sjorsansems/retro-alarm-clock/animations/beegees.gif

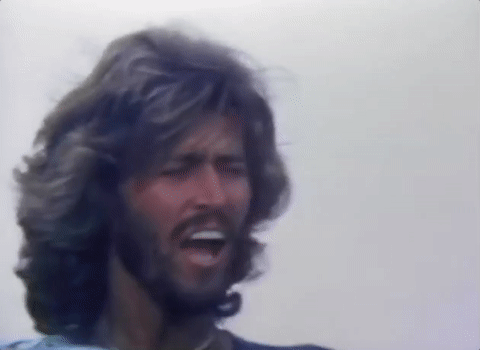
animations/beegees.gif
