sjorsansems/retro-alarm-clock/animations/fight.gif

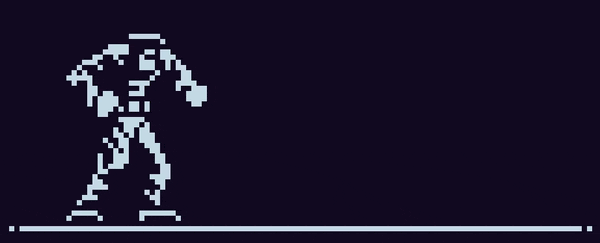
animations/fight.gif
