sjorsansems/retro-alarm-clock/animations/mk.gif

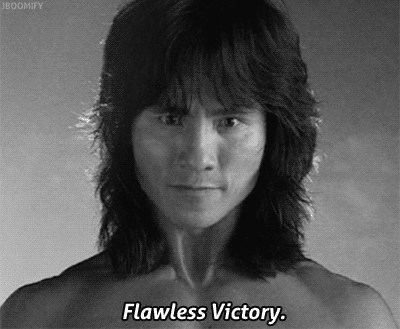
animations/mk.gif
