sjorsansems/retro-alarm-clock/retro_georgy_alarm_klok_v6_backup.py

"""
ESP32 Retro Georgy Alarm Clock (MicroPython)
Doel: stabiel draaien op lage RAM met WiFi + NTP + retro web UI + alarm animaties.
"""

from machine import Pin, SoftI2C
import framebuf
import time
import json
import network
import socket
import gc
import esp32

try:
    from urllib.parse import quote
except ImportError:
    quote = None

# Agressieve garbage collection en PSRAM setup
gc.enable()
gc.collect()
try:
    esp32.memory_info()
except:
    pass
try:
    gc.threshold(gc.mem_free() // 4 + gc.mem_alloc())
except:
    pass

LOW_MEMORY_WEB_MODE = False

# WLAN lazy init — niet pre-alloceren
_WLAN = None

try:
    from config_manager import ConfigManager
except ImportError:
    ConfigManager = None

try:
    from ntp_time_sync import NTPTimeSync
except ImportError:
    NTPTimeSync = None

try:
    from ds3231 import DS3231, AT24C32
except ImportError:
    DS3231 = None
    AT24C32 = None

try:
    from dfplayer import DFPlayer
except ImportError:
    DFPlayer = None

try:
    from neopixel_driver import NeopixelDriver
except ImportError:
    NeopixelDriver = None

# ESP32-S3 DevKitC-1 pinnen
SDA_PIN = 8   # gelabeld SDA op het board (OLED)
SCL_PIN = 9   # gelabeld SCL op het board (OLED)
DS3231_SDA_PIN = 5   # aparte I2C bus voor DS3231 RTC
DS3231_SCL_PIN = 6
I2C_FREQ = 100_000
# Buzzer uitgeschakeld — DFPlayer MP3 wordt gebruikt als alarm

# DFPlayer Mini: ESP32-S3 DevKitC-1
# GPIO17 = UART1 TX (gelabeld TXD1) -> 1kΩ -> DFPlayer RX
# GPIO18 = UART1 RX (gelabeld RXD1) <--------- DFPlayer TX
# Optioneel: BUSY-pin (actief-laag als er afgespeeld wordt)
DFPLAYER_UART_ID  = 1
DFPLAYER_TX_PIN   = 17
DFPLAYER_RX_PIN   = 18
DFPLAYER_BUSY_PIN = None   # bijv. 4 als je de BUSY-pin aansluit
DFPLAYER_TRACK    = 1      # track-nummer dat tijdens alarm afgespeeld wordt (1.mp3 op SD)

# WS2812B Addressable LEDs (8-LED strip)
WS2812_PIN = 2  # bevestigd werkend: GPIO2 + bitstream + GRB
WS2812_COUNT = 8  # 8 LEDs
WIDTH = 128
HEIGHT = 64
SH1106_COL_OFFSET = 2
WIFI_PORT = 80
WEBSERVER_START_DELAY_MS = 0
WIFI_MANUAL_ON_MS = 120000
WIFI_DAILY_CHECK_MS = 60000
WIFI_DAILY_RETRY_MS = 3600000
WIFI_MIN_FREE_HEAP = 35000
WIFI_CONNECT_TIMEOUT_S = 8
DEFAULT_WIFI_SSID = ""
WIFI_HOSTNAME = "alarmklok"
ALARM_INTRO_MS = 2500
ALARM_BOSS_MS = 20000
ALARM_AUTO_STOP_MS = 15 * 60 * 1000
NIGHT_DIM_START_HOUR = 22
NIGHT_DIM_END_HOUR = 7
UP_BUTTON_PIN = 13    # Touch13 / ADC2_2 — vrij op S3 DevKitC-1
DOWN_BUTTON_PIN = 12  # Touch12 / ADC2_1 — vrij
SET_BUTTON_PIN = 14   # Touch14 / ADC2_3 — vrij
DAY_KEYS = ("mon", "tue", "wed", "thu", "fri", "sat", "sun")

# Aantal MP3-nummers op de SD-kaart (lied 1 t/m N)
DFPLAYER_TRACK_COUNT = 30

# Koppel GIF-namen aan een alarm-tone (muziek + LEDs).
# Voeg hier nieuwe GIFs toe die je aan een specifiek liedje wilt koppelen.
# Waarde None = geen koppeling, gebruiker kiest zelf tone.
GIF_TONE_MAP = {
    "mario": "2",
    "zelda": "1",
    "doom":  None,
}


def get_alarm_tone_options():
    labels = {
        1: "Zelda", 2: "Mario", 3: "Synthwave", 4: "Sonic", 
        5: "Metroid", 6: "Pokemon", 7: "Tetris", 8: "Moonstone", 9: "Arcade"
    }
    schemes = {
        1: "Groen -> goud pulse",
        2: "Rood/geel checker",
        3: "Neon roze -> paars golf",
        4: "Cyaan/blauw strobe",
        5: "Oranje -> rood",
        6: "Geel met rode accenten",
        7: "Regenboog cyclus",
        8: "Maanblauw met fakkel-goud pulse",
        9: "Multicolor strobe",
    }
    return [
        {
            "key": str(i),
            "label": labels.get(i, "Lied {}".format(i)),
            "scheme": schemes.get(i, "Onbekend"),
        }
        for i in range(1, DFPLAYER_TRACK_COUNT + 1)
    ]


BIG_TIME_GLYPHS = {
    "0": ("111", "101", "101", "101", "111"),
    "1": ("010", "110", "010", "010", "111"),
    "2": ("111", "001", "111", "100", "111"),
    "3": ("111", "001", "111", "001", "111"),
    "4": ("101", "101", "111", "001", "001"),
    "5": ("111", "100", "111", "001", "111"),
    "6": ("111", "100", "111", "101", "111"),
    "7": ("111", "001", "001", "001", "001"),
    "8": ("111", "101", "111", "101", "111"),
    "9": ("111", "101", "111", "001", "111"),
    ":": ("0", "1", "0", "1", "0"),
}

_HTML_FILE = "index_v6.html"
_HTML_FILE_LITE = "index_lite.html"


def _send_all(sock, data):
    view = memoryview(data)
    while len(view):
        sent = sock.send(view)
        if sent is None or sent <= 0:
            break
        view = view[sent:]


def _send_html_response(sock, filename):
    _send_all(sock, b"HTTP/1.1 200 OK\r\nContent-Type: text/html\r\nConnection: close\r\n\r\n")
    try:
        with open(filename, "rb") as f:
            while True:
                chunk = f.read(512)
                if not chunk:
                    break
                _send_all(sock, chunk)
    except Exception as e:
        body = "<html><body>Fout: kan {} niet laden: {}</body></html>".format(filename, e)
        _send_all(sock, body.encode())


# HTML wordt van disk naar socket gestreamd via _send_html_response() - niet in RAM opgeslagen.
def enable_low_memory_web_mode():
    global LOW_MEMORY_WEB_MODE
    if LOW_MEMORY_WEB_MODE:
        return
    LOW_MEMORY_WEB_MODE = True
    gc.collect()


class SH1106_I2C(framebuf.FrameBuffer):
    def __init__(self, width, height, i2c, addr=0x3C):
        self.width = width
        self.height = height
        self.i2c = i2c
        self.addr = addr
        self.pages = height // 8
        self.buffer = bytearray(self.pages * width)
        super().__init__(self.buffer, width, height, framebuf.MONO_VLSB)
        for cmd in (0xAE, 0xD5, 0x80, 0xA8, self.height - 1, 0xD3, 0x00, 0x40,
                    0xAD, 0x8B, 0xA1, 0xC8, 0xDA, 0x12, 0x81, 0x7F, 0xD9, 0x22,
                    0xDB, 0x35, 0xA4, 0xA6, 0xAF):
            self.i2c.writeto(self.addr, bytes((0x80, cmd)))
        self.fill(0)
        self.show()

    def show(self):
        for page in range(self.pages):
            self.i2c.writeto(self.addr, bytes((0x80, 0xB0 + page)))
            col = SH1106_COL_OFFSET
            self.i2c.writeto(self.addr, bytes((0x80, col & 0x0F)))
            self.i2c.writeto(self.addr, bytes((0x80, 0x10 | (col >> 4))))
            start = self.width * page
            self.i2c.writeto(self.addr, b"\x40" + self.buffer[start:start + self.width])


class WiFiManagerLite:
    def __init__(self, ssid, password, timeout=WIFI_CONNECT_TIMEOUT_S):
        self.ssid = ssid
        self.password = password
        self.timeout = timeout
        global _WLAN
        if _WLAN is None:
            # Agressieve RAM cleanup voordat WiFi wordt geladen
            for _ in range(3):
                gc.collect()
                time.sleep(0.1)
            try:
                _WLAN = network.WLAN(network.STA_IF)
                # WLAN voorbij initi, nog niet actief
            except Exception as e:
                print("! WiFi pre-init fout, retrying...")
                for _ in range(5):
                    gc.collect()
                    time.sleep(0.1)
                try:
                    _WLAN = network.WLAN(network.STA_IF)
                except Exception:
                    raise OSError("WiFi Out of Memory")
        self.sta = _WLAN

    def connect(self):
        try:
            if self.sta.isconnected():
                return True
        except:
            pass

        if not self.ssid:
            print("! WiFi fout: SSID is leeg")
            return False

        try:
            # Minder agressief dan telkens active(False)->active(True),
            # want dat kan op sommige firmware builds instabiel zijn.
            if not self.sta.active():
                self.sta.active(True)
            time.sleep(0.5)

            # Zet een herkenbare netwerknaam voor DHCP/local DNS waar ondersteund.
            try:
                self.sta.config(dhcp_hostname=WIFI_HOSTNAME)
                print("WiFi hostname:", WIFI_HOSTNAME)
            except Exception:
                try:
                    network.hostname(WIFI_HOSTNAME)
                    print("WiFi hostname:", WIFI_HOSTNAME)
                except Exception:
                    pass

            # Begin met een schone connect-staat.
            try:
                self.sta.disconnect()
            except:
                pass

            print("WiFi: verbinden met '{}'...".format(self.ssid))
            self.sta.connect(self.ssid, self.password)
            start = time.ticks_ms()
            while not self.sta.isconnected():
                st = self.sta.status()
                # ESP32 statuscodes: -3 wrong password, -2 no AP, -1 fail
                if st in (-3, -2, -1):
                    if st == -3:
                        print("! WiFi fout: verkeerd wachtwoord")
                    elif st == -2:
                        print("! WiFi fout: SSID niet gevonden (2.4GHz?)")
                    else:
                        print("! WiFi fout: connect mislukt")
                    return False
                if time.ticks_diff(time.ticks_ms(), start) > self.timeout * 1000:
                    print("! WiFi timeout na {}s, status={}".format(self.timeout, self.sta.status()))
                    return False
                time.sleep(0.3)
                gc.collect()  # Agressieve GC tijdens connect
            ip = self.sta.ifconfig()[0]
            print("✓ WiFi verbonden, IP={}".format(ip))
            return True
        except KeyboardInterrupt:
            # Laat app doorlopen zonder crash als connect wordt onderbroken.
            print("! WiFi connect onderbroken")
            try:
                self.sta.disconnect()
            except:
                pass
            return False
        except Exception as e:
            print("! WiFi connect fout:", e)
            gc.collect()
            return False

    def is_connected(self):
        try:
            return self.sta and self.sta.isconnected()
        except:
            return False

    def get_ip(self):
        try:
            if self.is_connected():
                return self.sta.ifconfig()[0]
        except:
            pass
        return None


class ClockCore:
    def __init__(self, timezone_name="Europe/Amsterdam"):
        self.timezone_name = timezone_name
        self.soft_epoch = None
        self.soft_ticks = 0
        self.last_sync = 0
        self.rtc = None  # wordt gezet door App na I2C init

    @staticmethod
    def _is_leap_year(year):
        return (year % 4 == 0 and year % 100 != 0) or (year % 400 == 0)

    @staticmethod
    def _last_sunday_of_month(year, month):
        if month in (1, 3, 5, 7, 8, 10, 12):
            last_day = 31
        elif month in (4, 6, 9, 11):
            last_day = 30
        else:
            last_day = 29 if ClockCore._is_leap_year(year) else 28
        for day in range(last_day, 0, -1):
            wd = time.localtime(time.mktime((year, month, day, 12, 0, 0, 0, 0)))[6]  # 0=ma
            if wd == 6:  # zondag
                return day
        return last_day

    @staticmethod
    def _is_dst_nl(year, month, day):
        if month < 3 or month > 10:
            return False
        if 3 < month < 10:
            return True
        if month == 3:
            return day >= ClockCore._last_sunday_of_month(year, 3)
        return day < ClockCore._last_sunday_of_month(year, 10)

    @staticmethod
    def _utc_to_amsterdam(utc_tuple):
        y, m, d, hh, mm, ss = utc_tuple[:6]
        offset = 2 if ClockCore._is_dst_nl(y, m, d) else 1
        base = (y, m, d, hh, mm, ss, 0, 0)
        shifted = time.localtime(time.mktime(base) + offset * 3600)
        return (shifted[0], shifted[1], shifted[2], shifted[3], shifted[4], shifted[5], shifted[6] + 1, shifted[7])

    def _tz(self, utc_tuple):
        if self.timezone_name == "Europe/Amsterdam" and NTPTimeSync:
            t = NTPTimeSync.time_tuple_to_dutch(utc_tuple)
            if len(t) >= 7:
                t = t[:6] + (t[6] + 1,) + t[7:]
            return t, ("CEST" if NTPTimeSync.is_dst(utc_tuple[0], utc_tuple[1], utc_tuple[2]) else "CET")
        if self.timezone_name == "Europe/Amsterdam":
            t = self._utc_to_amsterdam(utc_tuple)
            return t, ("CEST" if self._is_dst_nl(utc_tuple[0], utc_tuple[1], utc_tuple[2]) else "CET")
        off = 0
        if self.timezone_name.startswith("UTC") and len(self.timezone_name) > 3:
            try:
                off = int(self.timezone_name[3:])
            except:
                off = 0
        base = (utc_tuple[0], utc_tuple[1], utc_tuple[2], utc_tuple[3], utc_tuple[4], utc_tuple[5], 0, 0)
        shifted = time.localtime(time.mktime(base) + off * 3600)
        return (shifted[0], shifted[1], shifted[2], shifted[3], shifted[4], shifted[5], shifted[6] + 1, shifted[7]), ("UTC" if off == 0 else "UTC{}{}".format("+" if off > 0 else "", off))

    def read_time(self):
        # Lees bij voorkeur rechtstreeks van DS3231
        if self.rtc is not None:
            try:
                t = self.rtc.datetime()   # (yr, mo, day, hr, min, sec, wd)
                # DS3231 bewaart in deze app al lokale tijd; niet opnieuw timezone-shiften.
                return (t[0], t[1], t[2], t[3], t[4], t[5], t[6], 0)
            except Exception:
                pass
        if self.soft_epoch is None:
            utc = time.gmtime()
            t, _ = self._tz(utc)
            self.set_time(*t[:6])
            return t
        elapsed = time.ticks_diff(time.ticks_ms(), self.soft_ticks) // 1000
        cur = time.localtime(self.soft_epoch + elapsed)
        return (cur[0], cur[1], cur[2], cur[3], cur[4], cur[5], cur[6] + 1, cur[7])

    def set_time(self, y, m, d, hh, mm, ss):
        base = (int(y), int(m), int(d), int(hh), int(mm), int(ss), 0, 0)
        self.soft_epoch = time.mktime(base)
        self.soft_ticks = time.ticks_ms()
        # Schrijf ook naar DS3231 als die beschikbaar is
        if self.rtc is not None:
            try:
                import time as _t
                wd = _t.localtime(self.soft_epoch)[6] + 1  # 1=ma
                self.rtc.set_datetime(int(y), int(m), int(d), int(hh), int(mm), int(ss), wd)
            except Exception as _e:
                print("! DS3231 schrijven mislukt:", _e)
        return True

    def set_timezone(self, name):
        self.timezone_name = name or "Europe/Amsterdam"
        utc = time.gmtime()
        t, _ = self._tz(utc)
        self.set_time(*t[:6])

    def sync_ntp(self):
        try:
            import ntptime
            ntptime.host = "pool.ntp.org"
            ntptime.settime()
            utc = time.gmtime()
            t, label = self._tz(utc)
            self.set_time(*t[:6])
            self.last_sync = time.time()
            print("✓ NTP Sync ({}) → ook naar DS3231 geschreven".format(label) if self.rtc else "✓ NTP Sync ({})".format(label))
            return True
        except Exception as e:
            print("✗ NTP Sync fout:", e)
            return False

    def timezone_label(self):
        t = self.read_time()
        if self.timezone_name == "Europe/Amsterdam" and NTPTimeSync:
            return "CEST" if NTPTimeSync.is_dst(t[0], t[1], t[2]) else "CET"
        return self.timezone_name


class App:
    def __init__(self):
        print("\n=== ESP32 RETRO GEORGY ALARM OPSTARTEN ===\n")
        self.config = ConfigManager("config.json") if ConfigManager else None
        self.tone = "1"
        self.volume = 70
        wifi_source = "fallback"
        if self.config:
            self.tone = self.config.get("alarm_sound", "tone", "1")
            self.volume = int(self.config.get("alarm_sound", "volume", 70) or 70)
            timezone = self.config.get("ntp", "timezone", "Europe/Amsterdam")
            raw_ssid = self.config.get("wifi", "ssid", None)
            raw_pwd = self.config.get("wifi", "password", None)
            ssid = str(raw_ssid or "").strip()
            pwd = str(raw_pwd or "")
            if ssid:
                wifi_source = "config.json"
            if getattr(self.config, "last_load_error", None):
                print("! Config waarschuwing:", self.config.last_load_error)
        else:
            timezone, ssid, pwd = "Europe/Amsterdam", "", ""

        if not ssid:
            ssid = DEFAULT_WIFI_SSID
            wifi_source = "defaults"

        print("WiFi cfg: '{}' ({})".format(ssid, wifi_source))
        self.wifi_ssid = ssid
        self.wifi_password = pwd
        self.tone = self._normalize_tone_key(self.tone)

        self.clock = ClockCore(timezone)
        self.alarm_until = None
        self.alarm_started_ms = None
        self.snooze_until = None
        self.snooze_tone = None
        self.snooze_gif = ""
        self.active_tone = self.tone
        self.active_gif = ""
        self._skip_intro = False
        self._in_intro = False
        self.alarm_edit_mode = False
        self.alarm_edit_last_change_ms = 0
        self.alarm_edit_hold_hint_until = 0
        self.alarm_edit_hour = 7
        self.alarm_edit_minute = 0
        self.alarm_edit_day_key = "mon"
        self._set_toggle_last_key = None
        self._set_feedback_text = ""
        self._set_feedback_until = 0
        self._set_feedback_lines = []
        self._intro_audio_playing = False
        self.last_schedule_fire = None
        self.alarm_schedule = self._default_alarm_schedule()
        if self.config:
            self.alarm_schedule = self._normalize_alarm_schedule(self.config.get("alarm_schedule", None, self.alarm_schedule))
        self.alarm_combo = self._default_alarm_combo()
        if self.config:
            self.alarm_combo = self._normalize_alarm_combo(self.config.get("alarm_combo", None, self.alarm_combo))
        self.alarm_gif_combo = self._default_alarm_gif_combo()
        if self.config:
            self.alarm_gif_combo = self._normalize_alarm_gif_combo(self.config.get("alarm_gif_combo", None, self.alarm_gif_combo))

        # GIF → toon koppeling (instelbaar via webinterface, opgeslagen in gif_tone_map.json)
        self._gif_tone_overrides = {}
        try:
            with open("gif_tone_map.json", "r") as _f:
                self._gif_tone_overrides = json.loads(_f.read())
        except Exception:
            pass

        # Track labels (instelbaar via webinterface, opgeslagen in track_labels.json)
        self._track_labels = {}
        try:
            with open("track_labels.json", "r") as _f:
                self._track_labels = json.loads(_f.read())
        except Exception:
            pass

        self.wifi = None
        self.wifi_ok = False
        self.wifi_disabled = False
        self.wifi_reconnect_after_ms = 0
        self.wifi_auto_off_ms = time.ticks_add(time.ticks_ms(), 30 * 60 * 1000)
        self.webserver_ready_after_ms = None
        self._ntp_synced_once = False
        self.startup_ip_until = None
        self.sock = None
        self.wifi_manual_until = None
        self.last_daily_sync_key = None
        self.next_daily_check_ms = time.ticks_add(time.ticks_ms(), WIFI_DAILY_CHECK_MS)
        self.next_daily_sync_attempt_ms = time.ticks_ms()
        self._display_dim_state = None
        self._display_manual_mode = 0  # 0=normaal, 1=dim, 2=extra dim
        self._weather_phase = 0
        self._rtc_temp = None
        self._rtc_temp_next_ms = 0
        self._weather_code = None      # WMO weathercode van Open-Meteo
        self._weather_temp = None      # buitentemperatuur °C (int)
        self._weather_next_ms = 0      # tijdstip eerste fetch (meteen bij opstart)
        self._weather_interval_ms = 6 * 3600 * 1000  # 4x per dag
        self._easter_active_until = None
        self._easter_message = ""
        self._easter_key = None
        # Klok-transitie animatie state
        self._transition_pending = True   # eerste keer na intro altijd animeren
        self._last_hour_shown = -1        # voor uur-omslag detectie
        self._transition_step = 0         # huidige frame binnen een lopende transitie
        self._transition_id = 0           # welke transitie (0-4)
        self._transition_active = False   # animatie bezig?
        self._transition_use_leds = True  # LEDs bij deze transitie? (False bij uur-omslag)
        self._transition_buf = None       # snapshot van klokscherm (bytearray 128×64/8)

        self.i2c = SoftI2C(sda=Pin(SDA_PIN, pull=Pin.PULL_UP), scl=Pin(SCL_PIN, pull=Pin.PULL_UP), freq=I2C_FREQ)
        self.display = None
        try:
            dev = self.i2c.scan()
            if 0x3C in dev:
                self.display = SH1106_I2C(WIDTH, HEIGHT, self.i2c, 0x3C)
        except:
            pass

        # DS3231 RTC initialiseren op eigen I2C bus (GPIO5/6)
        self.eeprom = None
        self.i2c_rtc = None
        if DS3231 is not None:
            try:
                self.i2c_rtc = SoftI2C(sda=Pin(DS3231_SDA_PIN, pull=Pin.PULL_UP), scl=Pin(DS3231_SCL_PIN, pull=Pin.PULL_UP), freq=I2C_FREQ)
                self.clock.rtc = DS3231(self.i2c_rtc)
                t = self.clock.rtc.datetime()
                print("✓ DS3231 gereed: {:04d}-{:02d}-{:02d} {:02d}:{:02d}:{:02d}".format(*t[:6]))
            except Exception as _e:
                print("! DS3231 niet gevonden:", _e)
                self.clock.rtc = None

        # AT24C32 EEPROM initialiseren (op dezelfde I2C bus als DS3231)
        if self.i2c_rtc is not None and AT24C32 is not None:
            try:
                self.eeprom = AT24C32(self.i2c_rtc)
                eeprom_schedule = self.eeprom.load_alarm_schedule()
                if eeprom_schedule is not None:
                    self.alarm_schedule = self._normalize_alarm_schedule(eeprom_schedule)
                    print("✓ Alarmschema geladen uit EEPROM")
                else:
                    print("✓ AT24C32 gereed (geen opgeslagen schema)")
            except Exception as _e:
                print("! AT24C32 niet gevonden:", _e)
                self.eeprom = None

        # DFPlayer/WS2812 lazy init: pas initialiseren zodra alarm start.
        self.dfplayer = None
        self._dfplayer_failed = False
        self._dfplayer_playing = False

        self.leds = None
        self._leds_failed = False
        self._led_sunrise_active = False
        self._nightlight_on = False

        # GIF-animatie state (alarm)
        self._gif_file = None
        self._gif_n_frames = 0
        self._gif_frame_size = 0
        self._gif_delays = []
        self._gif_cur_frame = 0
        self._gif_next_ms = 0
        self._gif_data_offset = 0

        # Zorg dat de strip direct bij boot in een bekende UIT-toestand staat.
        self._ensure_leds_ready()
        if self.leds is not None:
            try:
                self.leds.clear()
            except Exception:
                pass

        self.btn_up = Pin(UP_BUTTON_PIN, Pin.IN, Pin.PULL_UP)
        self.btn_down = Pin(DOWN_BUTTON_PIN, Pin.IN, Pin.PULL_UP)
        self.btn_set = Pin(SET_BUTTON_PIN, Pin.IN, Pin.PULL_UP)
        # start=tijdstip indrukken, fired_long=lange druk al uitgevoerd,
        # last_edge=debounce timestamp, pending=actie klaar voor uitvoering
        self._button_state = {
            "set":  {"start": 0, "fired_long": False, "last_edge": 0, "pending": None},
            "up":   {"start": 0, "fired_long": False, "last_edge": 0, "pending": None},
            "down": {"start": 0, "fired_long": False, "last_edge": 0, "pending": None},
        }

        # Hardware IRQ op falling + rising edge:
        # - UP heeft geen lange druk → vuurt pending="short" direct bij indrukken
        # - SET/DOWN wachten tot loslaten om te bepalen of het kort of lang was
        _bs = self._button_state
        def _make_irq(name, has_long_cb):
            s = _bs[name]
            def handler(p):
                now = time.ticks_ms()
                if time.ticks_diff(now, s["last_edge"]) < 40:
                    return
                s["last_edge"] = now
                if p.value() == 0:  # falling edge = ingedrukt
                    s["start"] = now
                    s["fired_long"] = False
                    if not has_long_cb:
                        s["pending"] = "short"  # direct actie op druk
                    # SET knop tijdens intro -> alleen overslaan (geen short/long actie na intro).
                    if name == "set" and self._in_intro:
                        self._skip_intro = True
                        s["pending"] = None
                        s["fired_long"] = True
                else:  # rising edge = losgelaten
                    if has_long_cb and not s["fired_long"]:
                        s["pending"] = "short"  # was een korte druk
            return handler
        self.btn_up.irq(trigger=Pin.IRQ_FALLING | Pin.IRQ_RISING, handler=_make_irq("up", False))
        self.btn_down.irq(trigger=Pin.IRQ_FALLING | Pin.IRQ_RISING, handler=_make_irq("down", True))
        self.btn_set.irq(trigger=Pin.IRQ_FALLING | Pin.IRQ_RISING, handler=_make_irq("set", True))

        print("WiFi: verbinden...")
        gc.collect()
        gc.collect()
        if self._ensure_wifi_connected():
            self.clock.sync_ntp()
            self._ntp_synced_once = True
            t2 = self.clock.read_time()
            self.last_daily_sync_key = (int(t2[0]), int(t2[1]), int(t2[2]))
        else:
            print("WiFi: niet verbonden bij opstarten")
        self._apply_display_brightness(force=True)

    def _prepare_for_wifi_attempt(self):
        gc.collect()
        gc.collect()
        gc.collect()

    def _ensure_dfplayer_ready(self):
        if self.dfplayer is not None or self._dfplayer_failed or DFPlayer is None:
            return self.dfplayer is not None
        try:
            dfvol = max(0, min(30, int(self.volume * 30 // 100)))
            self.dfplayer = DFPlayer(
                uart_id=DFPLAYER_UART_ID,
                tx_pin=DFPLAYER_TX_PIN,
                rx_pin=DFPLAYER_RX_PIN,
                busy_pin=DFPLAYER_BUSY_PIN,
                volume=dfvol,
            )
            print("✓ DFPlayer Mini gereed (volume {})".format(dfvol))
            return True
        except Exception as e:
            print("! DFPlayer init mislukt:", e)
            self._dfplayer_failed = True
            self.dfplayer = None
            gc.collect()
            return False

    def _ensure_leds_ready(self):
        if self.leds is not None or self._leds_failed or NeopixelDriver is None:
            return self.leds is not None
        try:
            self.leds = NeopixelDriver(pin=WS2812_PIN, num_leds=WS2812_COUNT)
            self.leds.set_brightness(92)  # 36% brightness om stroom-problemen te voorkomen
            self.leds.clear()
            print("✓ WS2812B LEDs gereed (GPIO{}, {} LEDs)".format(WS2812_PIN, WS2812_COUNT))
            return True
        except Exception as e:
            print("! WS2812B init mislukt:", e)
            self._leds_failed = True
            self.leds = None
            gc.collect()
            return False

    def _close_webserver(self):
        try:
            if self.sock:
                self.sock.close()
        except:
            pass
        self.sock = None

    def _disable_wifi(self):
        self._close_webserver()
        try:
            if self.wifi and self.wifi.sta:
                try:
                    self.wifi.sta.disconnect()
                except:
                    pass
                try:
                    self.wifi.sta.active(False)
                except:
                    pass
        except:
            pass
        self.wifi_ok = False

    def _ensure_wifi_connected(self):
        gc.collect()
        self.wifi_ok = False
        try:
            if self.wifi is None:
                self.wifi = WiFiManagerLite(self.wifi_ssid, self.wifi_password, timeout=WIFI_CONNECT_TIMEOUT_S)
            self.wifi_ok = self.wifi.connect()
        except KeyboardInterrupt:
            self.wifi_ok = False
            print("! WiFi poging onderbroken")
            return False
        except Exception as e:
            self.wifi_ok = False
            print("! WiFi fout:", e)
            msg = str(e)
            if "Out of Memory" in msg or "Memory" in msg:
                # Bij WiFi OOM: web UI in low-memory modus, WiFi object vrijgeven,
                # en pas later opnieuw proberen.
                enable_low_memory_web_mode()
                self._disable_wifi()
                self.wifi = None
                self.wifi_reconnect_after_ms = time.ticks_add(time.ticks_ms(), 180000)
                print("! WiFi OOM: volgende poging over 3 minuten")
            gc.collect()
            return False

        if self.wifi_ok:
            self.startup_ip_until = time.ticks_add(time.ticks_ms(), 5000)
            self.webserver_ready_after_ms = time.ticks_add(time.ticks_ms(), WEBSERVER_START_DELAY_MS)
            self._start_webserver_if_ready()
            return True
        return False

    def _start_webserver_if_ready(self):
        if not self.wifi_ok or self.sock is not None:
            return

        if self.webserver_ready_after_ms is not None and time.ticks_diff(time.ticks_ms(), self.webserver_ready_after_ms) < 0:
            return

        ip = self.wifi.get_ip() if self.wifi else "0.0.0.0"
        try:
            self.sock = socket.socket(socket.AF_INET, socket.SOCK_STREAM)
            self.sock.setsockopt(socket.SOL_SOCKET, socket.SO_REUSEADDR, 1)
            self.sock.bind(("0.0.0.0", WIFI_PORT))
            self.sock.listen(2)
            self.sock.settimeout(0)
            print("Web:", "http://{}".format(ip))
        except Exception as e:
            print("! Webserver start fout:", e)
            try:
                if self.sock:
                    self.sock.close()
            except:
                pass
            self.sock = None
            self.webserver_ready_after_ms = time.ticks_add(time.ticks_ms(), 5000)

    def _handle_wifi_state(self):
        now = time.ticks_ms()

        # Auto-off na 30 minuten na opstarten
        if not self.wifi_disabled and self.wifi_auto_off_ms is not None and time.ticks_diff(now, self.wifi_auto_off_ms) >= 0:
            self.wifi_auto_off_ms = None
            self._disable_wifi()
            self.wifi_disabled = True
            print("WiFi auto-uit na 30 min")

        # WiFi altijd aan (tenzij handmatig uitgeschakeld): herverbinden als nodig
        if not self.wifi_disabled:
            if not self.wifi_ok or not self.wifi or not self.wifi.is_connected():
                # Maximaal 1x per 30 sec proberen (voorkomt blokkering elke loop-cycle)
                if time.ticks_diff(now, self.wifi_reconnect_after_ms) >= 0:
                    self._ensure_wifi_connected()
                    self.wifi_reconnect_after_ms = time.ticks_add(now, 30000)
            self._start_webserver_if_ready()

        if time.ticks_diff(now, self.next_daily_check_ms) >= 0:
            self.next_daily_check_ms = time.ticks_add(now, WIFI_DAILY_CHECK_MS)
            t = self.clock.read_time()
            day_key = (int(t[0]), int(t[1]), int(t[2]))
            # Dagelijkse NTP sync om 12:00: WiFi aan, sync, WiFi uit
            if int(t[3]) >= 12 and self.last_daily_sync_key != day_key and time.ticks_diff(now, self.next_daily_sync_attempt_ms) >= 0:
                print("Dagelijkse NTP sync (12:00)...")
                if self._ensure_wifi_connected() and self.clock.sync_ntp():
                    t2 = self.clock.read_time()
                    self.last_daily_sync_key = (int(t2[0]), int(t2[1]), int(t2[2]))
                    self.next_daily_sync_attempt_ms = now
                    print("Dagelijkse sync OK, WiFi weer uit")
                else:
                    self.next_daily_sync_attempt_ms = time.ticks_add(now, WIFI_DAILY_RETRY_MS)
                    print("Dagelijkse sync mislukt, volgende poging over 1 uur")
                # Altijd WiFi uitzetten na de sync poging
                self._disable_wifi()
                self.wifi_disabled = True
                self.wifi_auto_off_ms = None

    def _default_alarm_schedule(self):
        return {k: {"enabled": False, "hour": 7, "minute": 0} for k in DAY_KEYS}

    def _default_alarm_combo(self):
        # Per dag een vaste track/scene-combo.
        return {
            "mon": "1", "tue": "2", "wed": "3", "thu": "1",
            "fri": "2", "sat": "3", "sun": "1",
        }

    def _normalize_alarm_combo(self, raw):
        out = self._default_alarm_combo()
        if not isinstance(raw, dict):
            return out
        for k in DAY_KEYS:
            out[k] = self._normalize_tone_key(raw.get(k, out[k]))
        return out

    def _default_alarm_gif_combo(self):
        # Standaard: per dag willekeurige GIF-animatie.
        return {k: "random" for k in DAY_KEYS}

    def _normalize_alarm_gif_combo(self, raw):
        out = self._default_alarm_gif_combo()
        if not isinstance(raw, dict):
            return out
        for k in DAY_KEYS:
            val = raw.get(k, "random")
            if isinstance(val, str):
                safe = "".join(c for c in val if ('a' <= c <= 'z') or ('A' <= c <= 'Z') or ('0' <= c <= '9') or c in ('-', '_'))
                safe = safe[:32]
                out[k] = safe if safe else "random"
        return out

    def _get_gif_tone(self, gif_name):
        """Geeft de gekoppelde toon-key voor een GIF, overrides hebben prioriteit."""
        if gif_name in self._gif_tone_overrides:
            return self._gif_tone_overrides[gif_name]
        return GIF_TONE_MAP.get(gif_name)

    def _save_track_labels(self):
        try:
            with open("track_labels.json", "w") as _f:
                _f.write(json.dumps(self._track_labels))
        except Exception as _e:
            print("! track_labels.json schrijven mislukt:", _e)

    def _save_gif_tone_overrides(self):
        try:
            with open("gif_tone_map.json", "w") as _f:
                _f.write(json.dumps(self._gif_tone_overrides))
        except Exception as _e:
            print("! gif_tone_map.json schrijven mislukt:", _e)

    def _merged_gif_tone_map(self):
        merged = {k: v for k, v in GIF_TONE_MAP.items() if v is not None}
        merged.update({k: v for k, v in self._gif_tone_overrides.items() if v})
        return merged

    def _list_gif_names(self):
        import os as _os
        names = []
        for path in ('/', '.'):
            try:
                names = [f[:-4] for f in _os.listdir(path) if isinstance(f, str) and f.endswith('.bin')]
                if names:
                    break
            except Exception:
                pass
        return sorted(set(names))

    def _list_gif_choices(self):
        # 'random' altijd als expliciete optie in UI/API.
        return ["random"] + self._list_gif_names()

    def _get_storage_info(self):
        # Geeft opslagstatus terug zodat web UI upload-limiet kan bewaken.
        try:
            import os as _os
            st = _os.statvfs('/')
            block_size = int(st[0])
            total_bytes = block_size * int(st[2])
            free_bytes = block_size * int(st[3])
            used_bytes = max(0, total_bytes - free_bytes)
            reserve_bytes = 128 * 1024  # buffer om crashes door volle flash te voorkomen
            upload_max_bytes = max(0, free_bytes - reserve_bytes)
            percent_used = int((used_bytes * 100) // total_bytes) if total_bytes > 0 else 0
            return {
                "total_bytes": total_bytes,
                "used_bytes": used_bytes,
                "free_bytes": free_bytes,
                "reserve_bytes": reserve_bytes,
                "upload_max_bytes": upload_max_bytes,
                "percent_used": percent_used,
            }
        except Exception:
            return {
                "total_bytes": 0,
                "used_bytes": 0,
                "free_bytes": 0,
                "reserve_bytes": 0,
                "upload_max_bytes": 0,
                "percent_used": 0,
            }

    def _pick_alarm_gif(self, gif_setting):
        if not isinstance(gif_setting, str):
            return ""
        if gif_setting == "random":
            names = self._list_gif_names()
            if not names:
                return ""
            # Lichtgewicht pseudo-random keuze zonder extra modules.
            t = self.clock.read_time()
            seed = (int(t[0]) * 1000000) + (int(t[1]) * 10000) + (int(t[2]) * 100) + int(t[5])
            seed ^= int(time.ticks_ms())
            idx = seed % len(names)
            return names[idx]
        return gif_setting

    def _normalize_alarm_schedule(self, raw):
        out = self._default_alarm_schedule()
        if not isinstance(raw, dict):
            return out
        for k in DAY_KEYS:
            row = raw.get(k, {}) if isinstance(raw.get(k, {}), dict) else {}
            out[k]["enabled"] = bool(row.get("enabled", False))
            out[k]["hour"] = int(row.get("hour", 7)) % 24
            out[k]["minute"] = int(row.get("minute", 0)) % 60
        return out

    def _check_scheduled_alarm(self):
        if self.alarm_until is not None:
            return
        t = self.clock.read_time()
        day_key = DAY_KEYS[(int(t[6]) - 1) % 7]
        sch = self.alarm_schedule.get(day_key, {})
        if not sch.get("enabled", False):
            return
        if int(sch.get("hour", -1)) != int(t[3]) or int(sch.get("minute", -1)) != int(t[4]):
            return
        fire_key = (t[0], t[1], t[2], t[3], t[4])
        if self.last_schedule_fire == fire_key:
            return
        self.last_schedule_fire = fire_key
        self.snooze_until = None
        self.snooze_tone = None
        self.snooze_gif = ""
        self.active_tone = self._normalize_tone_key(self.alarm_combo.get(day_key, self._tone_now()))
        self.active_gif = self._pick_alarm_gif(self.alarm_gif_combo.get(day_key, "random"))
        # Overschrijf tone als de gekozen GIF een vaste koppeling heeft
        if self.active_gif and self._get_gif_tone(self.active_gif) is not None:
            self.active_tone = self._normalize_tone_key(self._get_gif_tone(self.active_gif))
            print("GIF-tone koppeling: {} -> tone {}".format(self.active_gif, self.active_tone))
        self.alarm_started_ms = time.ticks_ms()
        self.alarm_until = time.ticks_add(time.ticks_ms(), ALARM_AUTO_STOP_MS)

    def _stop_alarm(self):
        self.alarm_until = None
        self.alarm_started_ms = None
        self._nightlight_on = False  # alarm overschrijft nachtlampje
        if self.dfplayer is not None:
            try:
                self.dfplayer.stop()
                self.dfplayer.set_volume(0)  # dempt idle ticking
            except Exception:
                pass
        self._dfplayer_playing = False
        self._intro_audio_playing = False
        if self.leds is not None:
            try:
                self.leds.clear()
            except Exception:
                pass
        self._led_sunrise_active = False
        self.active_gif = ""
        # Sluit eventueel open GIF-bestand
        if self._gif_file is not None:
            try:
                self._gif_file.close()
            except Exception:
                pass
            self._gif_file = None
            self._gif_delays = []

    def _snooze_alarm(self, minutes=10):
        if self.alarm_until is None:
            return
        self.snooze_tone = self.active_tone
        self.snooze_gif = self.active_gif
        self._stop_alarm()
        self.snooze_until = time.ticks_add(time.ticks_ms(), int(minutes) * 60 * 1000)
        self._set_feedback("SNOOZE 10 MIN", ms=2000)
        print("Alarm snooze {} min".format(int(minutes)))

    def _snooze_remaining_seconds(self):
        if self.snooze_until is None:
            return 0
        rem_ms = time.ticks_diff(self.snooze_until, time.ticks_ms())
        if rem_ms <= 0:
            return 0
        return (rem_ms + 999) // 1000

    def _current_day_alarm(self):
        t = self.clock.read_time()
        day_idx = (int(t[6]) - 1) % 7
        day_key = DAY_KEYS[day_idx]
        row = self.alarm_schedule.get(day_key, {"enabled": False, "hour": 7, "minute": 0})
        return day_key, row

    def _set_feedback(self, text, ms=2200):
        self._set_feedback_text = str(text or "")
        self._set_feedback_until = time.ticks_add(time.ticks_ms(), int(ms))

    def _next_alarm_entry(self, include_disabled=False):
        t = self.clock.read_time()
        day_abbr = ("ma", "di", "wo", "do", "vr", "za", "zo")
        day_keys = ("mon", "tue", "wed", "thu", "fri", "sat", "sun")
        cfg = self.alarm_schedule
        if not isinstance(cfg, dict):
            return None
        today_idx = (int(t[6]) - 1) % 7
        cur_h = int(t[3])
        cur_m = int(t[4])
        for offset in range(7):
            di = (today_idx + offset) % 7
            key = day_keys[di]
            alarm = cfg.get(key)
            if alarm is None:
                continue
            enabled = bool(alarm.get("enabled", False))
            if (not include_disabled) and (not enabled):
                continue
            try:
                hh = int(alarm.get("hour", 0))
                mm = int(alarm.get("minute", 0))
            except Exception:
                continue
            if offset == 0 and (hh < cur_h or (hh == cur_h and mm <= cur_m)):
                continue
            return {
                "key": key,
                "day": day_abbr[di],
                "hour": hh,
                "minute": mm,
                "enabled": enabled,
            }
        return None

    def _set_toggle_next_alarm(self):
        day_map = {
            "mon": "maandag", "tue": "dinsdag", "wed": "woensdag",
            "thu": "donderdag", "fri": "vrijdag", "sat": "zaterdag", "sun": "zondag"
        }
        # Tweede druk na UIT: zet exact die eerder uitgezette alarmdag weer AAN.
        if self._set_toggle_last_key:
            row = self.alarm_schedule.get(self._set_toggle_last_key)
            if isinstance(row, dict) and (not bool(row.get("enabled", False))):
                hh = int(row.get("hour", 7)) % 24
                mm = int(row.get("minute", 0)) % 60
                self.alarm_schedule[self._set_toggle_last_key] = {
                    "enabled": True, "hour": hh, "minute": mm,
                }
                if self.config:
                    self.config.config["alarm_schedule"] = self.alarm_schedule
                    self.config.save()
                if self.eeprom is not None:
                    try:
                        self.eeprom.save_alarm_schedule(self.alarm_schedule)
                    except Exception:
                        pass
                day_txt = day_map.get(self._set_toggle_last_key, self._set_toggle_last_key)
                nxt_after = self._next_alarm_entry(include_disabled=False)
                lines = [
                    "Alarm aan op:",
                    "{} {:02d}:{:02d}".format(day_txt, hh, mm),
                    "---",
                ]
                if nxt_after:
                    nxt_day = day_map.get(nxt_after["key"], nxt_after["day"])
                    lines += [
                        "Eerst volgend:",
                        "{} {:02d}:{:02d}".format(nxt_day, nxt_after["hour"], nxt_after["minute"]),
                    ]
                else:
                    lines += ["Geen volgend", "alarm actief"]
                self._set_feedback_lines = lines
                self._set_feedback("", ms=3500)
                print("Alarm AAN {} {:02d}:{:02d}".format(day_txt, hh, mm))
                self._set_toggle_last_key = None
                return

        # Eerste druk: zet eerstvolgende actieve alarm UIT.
        nxt = self._next_alarm_entry(include_disabled=False)
        if not nxt:
            self._set_feedback_lines = ["Geen actief", "alarm gevonden"]
            self._set_feedback("", ms=2500)
            print("Geen actief alarm om UIT te zetten")
            return

        key = nxt["key"]
        row = self.alarm_schedule.get(key, {})
        hh = int(row.get("hour", nxt["hour"])) % 24
        mm = int(row.get("minute", nxt["minute"])) % 60
        self.alarm_schedule[key] = {"enabled": False, "hour": hh, "minute": mm}
        if self.config:
            self.config.config["alarm_schedule"] = self.alarm_schedule
            self.config.save()
        if self.eeprom is not None:
            try:
                self.eeprom.save_alarm_schedule(self.alarm_schedule)
            except Exception:
                pass
        self._set_toggle_last_key = key
        day_txt = day_map.get(key, nxt["day"])
        nxt_after = self._next_alarm_entry(include_disabled=False)
        lines = [
            "Alarm uit op:",
            "{} {:02d}:{:02d}".format(day_txt, hh, mm),
            "---",
        ]
        if nxt_after:
            nxt_day = day_map.get(nxt_after["key"], nxt_after["day"])
            lines += [
                "Eerst volgend:",
                "{} {:02d}:{:02d}".format(nxt_day, nxt_after["hour"], nxt_after["minute"]),
            ]
        else:
            lines += ["Geen volgend", "alarm actief"]
        self._set_feedback_lines = lines
        self._set_feedback("", ms=3500)
        print("Alarm UIT {} {:02d}:{:02d}".format(day_txt, hh, mm))

    def _toggle_today_alarm(self):
        day_key, row = self._current_day_alarm()
        enabled = not bool(row.get("enabled", False))
        self.alarm_schedule[day_key] = {
            "enabled": enabled,
            "hour": int(row.get("hour", 7)) % 24,
            "minute": int(row.get("minute", 0)) % 60,
        }
        if self.config:
            self.config.config["alarm_schedule"] = self.alarm_schedule
            self.config.save()
        if self.eeprom is not None:
            try:
                self.eeprom.save_alarm_schedule(self.alarm_schedule)
            except Exception:
                pass
        print("Alarm {} {} {:02d}:{:02d}".format("AAN" if enabled else "UIT", day_key, self.alarm_schedule[day_key]["hour"], self.alarm_schedule[day_key]["minute"]))

    def _enter_alarm_edit_mode(self):
        day_key, row = self._current_day_alarm()
        self.alarm_edit_mode = True
        self.alarm_edit_last_change_ms = 0
        self.alarm_edit_hold_hint_until = 0
        self.alarm_edit_day_key = day_key
        self.alarm_edit_hour = int(row.get("hour", 7)) % 24
        self.alarm_edit_minute = int(row.get("minute", 0)) % 60
        print("Alarm instellen {} {:02d}:{:02d}".format(day_key, self.alarm_edit_hour, self.alarm_edit_minute))
        self._ensure_leds_ready()
        if self.leds:
            for i in range(self.leds.num_leds):
                self.leds.set_pixel(i, 60, 0, 0)  # dim rood
            self.leds.show()

    def _save_alarm_edit_mode(self):
        self.alarm_schedule[self.alarm_edit_day_key] = {
            "enabled": True,
            "hour": int(self.alarm_edit_hour) % 24,
            "minute": int(self.alarm_edit_minute) % 60,
        }
        self.alarm_edit_mode = False
        self.alarm_edit_hold_hint_until = 0
        if self.config:
            self.config.config["alarm_schedule"] = self.alarm_schedule
            self.config.save()
        if self.eeprom is not None:
            try:
                self.eeprom.save_alarm_schedule(self.alarm_schedule)
            except Exception:
                pass
        print("Alarm opgeslagen {} {:02d}:{:02d}".format(self.alarm_edit_day_key, self.alarm_edit_hour, self.alarm_edit_minute))
        self._play_alarm_saved_animation()
        self._start_clock_transition(use_leds=True)

    def _play_alarm_saved_animation(self):
        if not self.display:
            return
        # Korte, goedkope 8-bit save animatie met rode LED knipper.
        seed = (time.ticks_ms() ^ (self.alarm_edit_hour << 8) ^ self.alarm_edit_minute) & 0x7FFFFFFF
        for fi in range(22):
            self.display.fill(0)
            if fi % 4 < 2:
                self.display.rect(0, 0, 128, 64, 1)
            # 8-bit sterretjes (lichte random sparkle)
            for _i in range(10):
                seed = (1103515245 * seed + 12345) & 0x7FFFFFFF
                x = (seed >> 8) % 128
                seed = (1103515245 * seed + 12345) & 0x7FFFFFFF
                y = (seed >> 16) % 64
                self.display.pixel(x, y, 1)
            if fi >= 4:
                self.display.text("TIJD", 40, 20, 1)
            if fi >= 8:
                self.display.text("OPGESLAGEN", 24, 34, 1)
            if fi >= 12 and (fi % 2 == 0):
                self.display.text("OK", 56, 50, 1)
            self.display.show()

            if self.leds:
                if fi % 2 == 0:
                    for j in range(self.leds.num_leds):
                        self.leds.set_pixel(j, 80, 0, 0)
                    self.leds.show()
                else:
                    self.leds.clear()
            time.sleep_ms(70)

        if self.leds:
            if self._nightlight_on:
                for i in range(self.leds.num_leds):
                    self.leds.set_pixel(i, 255, 120, 40)
                self.leds.show()
            else:
                self.leds.clear()

    def _set_short_press(self):
        if self.alarm_until is not None:
            self._stop_alarm()
            return
        if self.alarm_edit_mode:
            self.alarm_edit_hold_hint_until = time.ticks_add(time.ticks_ms(), 3000)
            return
        self._set_toggle_next_alarm()

    def _set_long_press(self):
        if self.alarm_until is not None:
            self._stop_alarm()
            return
        if self.alarm_edit_mode:
            self._save_alarm_edit_mode()
            return
        self._enter_alarm_edit_mode()

    def _up_short_press(self):
        if self.alarm_edit_mode:
            self.alarm_edit_hour = (self.alarm_edit_hour + 1) % 24
            self.alarm_edit_last_change_ms = time.ticks_ms()
            return
        # Normaal scherm: nachtlampje aan/uit
        self._nightlight_on = not self._nightlight_on
        self._ensure_leds_ready()
        if self.leds:
            if self._nightlight_on:
                # Warm wit, laag vermogen (~30% brightness)
                for i in range(self.leds.num_leds):
                    self.leds.set_pixel(i, 255, 120, 40)
                self.leds.show()
                print("Nachtlampje AAN")
            else:
                self.leds.clear()
                print("Nachtlampje UIT")

    def _down_short_press(self):
        if self.alarm_until is not None:
            self._snooze_alarm(10)
            return
        if not self.alarm_edit_mode:
            self._display_manual_mode = (self._display_manual_mode + 1) % 3
            labels = ("OLED: NORMAAL", "OLED: DIM", "OLED: RAND")
            self._set_feedback(labels[self._display_manual_mode], ms=1200)
            self._apply_display_brightness(force=True)
            return
        self.alarm_edit_minute = (self.alarm_edit_minute + 1) % 60
        self.alarm_edit_last_change_ms = time.ticks_ms()

    def _down_long_press(self):
        if self.alarm_until is not None:
            self._stop_alarm()
            return
        if self.alarm_edit_mode:
            return

        if self.wifi_disabled:
            # WiFi was uit: zet aan en reset auto-off timer
            self.wifi_disabled = False
            self.wifi_auto_off_ms = time.ticks_add(time.ticks_ms(), 30 * 60 * 1000)
            print("WiFi AAN (auto-uit over 30 min)")
            if self._ensure_wifi_connected():
                ip = self.wifi.get_ip() if self.wifi else None
                print("WiFi verbonden:", ip if ip else "geen IP")
        else:
            # WiFi was aan: zet uit en annuleer auto-off timer
            self._disable_wifi()
            self.wifi_disabled = True
            self.wifi_auto_off_ms = None
            print("WiFi UIT")

    def _handle_buttons(self):
        now = time.ticks_ms()
        buttons = [
            ("set",  self._set_short_press,  self._set_long_press,  self.btn_set,  3000),
            ("up",   self._up_short_press,    None,                  self.btn_up,   0),
            ("down", self._down_short_press,  self._down_long_press, self.btn_down, 3000),
        ]
        for name, short_cb, long_cb, pin_obj, long_ms in buttons:
            s = self._button_state[name]

            # Alarm actief: SET stopt, DOWN snooze 10 min, UP doet niets.
            if s["pending"] is not None and self.alarm_until is not None:
                s["pending"] = None
                s["fired_long"] = True
                if name == "set":
                    self._stop_alarm()
                elif name == "down":
                    self._snooze_alarm(10)
                continue

            # Voer pending actie direct uit (gezet door IRQ)
            if s["pending"] == "short":
                s["pending"] = None
                if short_cb:
                    short_cb()
            elif s["pending"] == "long":
                s["pending"] = None
                if long_cb:
                    long_cb()

            # Lange druk detectie terwijl knop ingehouden (alleen voor knoppen met long_cb)
            if long_cb and not s["fired_long"] and pin_obj.value() == 0:
                if s["start"] > 0 and time.ticks_diff(now, s["start"]) >= long_ms:
                    s["fired_long"] = True
                    s["pending"] = None  # annuleer eventuele short
                    long_cb()

    def _normalize_tone_key(self, tone):
        try:
            n = int(tone)
            if 1 <= n <= DFPLAYER_TRACK_COUNT:
                return str(n)
        except (ValueError, TypeError):
            pass
        return "1"

    def _tone_now(self):
        return self._normalize_tone_key(self.tone)

    def _alarm_elapsed_ms(self):
        if self.alarm_started_ms is None:
            return 0
        return max(0, time.ticks_diff(time.ticks_ms(), self.alarm_started_ms))

    def _alarm_boss_level(self):
        ms = self._alarm_elapsed_ms()
        if ms < ALARM_BOSS_MS:
            return 0
        if ms < ALARM_BOSS_MS + 15000:
            return 1
        if ms < ALARM_BOSS_MS + 30000:
            return 2
        return 3

    def _alarm_intensity(self):
        # Intensity is used by LED and animation themes as a 0-100 value.
        ms = self._alarm_elapsed_ms()
        base = 25 + (ms // 1000)  # ramps up about 1% per second
        base += self._alarm_boss_level() * 10
        if base > 100:
            return 100
        if base < 0:
            return 0
        return int(base)

    def _play(self, now_ms):
        if self.alarm_started_ms is None:
            self.alarm_started_ms = now_ms

        # Initialiseer DFPlayer pas wanneer alarm echt start.
        df_ready = self._ensure_dfplayer_ready()
        if not df_ready and DFPlayer is not None and not self._dfplayer_failed:
            print("! DFPlayer niet klaar voor alarmstart")

        # --- DFPlayer: herhaal het geselecteerde lied totdat alarm eindigt ---
        if self.dfplayer is not None:
            try:
                track = int(self.active_tone)
                dfvol = max(0, min(30, int(self.volume * 30 // 100) + self._alarm_boss_level() * 3))
                self.dfplayer.set_volume(dfvol)
                
                # Speel altijd: dit zorgt ervoor dat als het nummer is afgelopen, het opnieuw start
                if not self._dfplayer_playing:
                    self.dfplayer.play_mp3(track)
                    print("DFPlayer: speel track {} op volume {}".format(track, dfvol))
                    self._dfplayer_playing = True
                else:
                    # Muziek loopt. Check elke seconde of we opnieuw moeten starten
                    # (DFPlayer geeft geen status terug, dus we spelen gewoon opnieuw)
                    pass
            except Exception as e:
                print("! DFPlayer play fout:", e)
            return

        # Geen DFPlayer beschikbaar: stil (buzzer uitgeschakeld)
        return

    def _update_led_animation(self, frame):
        """Update WS2812B LED animations during alarm."""
        self._ensure_leds_ready()
        if not self.leds:
            return

        tone = getattr(self, 'active_tone', '1')
        intensity = self._alarm_intensity()

        # Per-tone theme should start immediately when alarm starts.
        self._led_sunrise_active = False

        # Get theme function and play animation
        try:
            theme_func = self.leds.get_theme_func(tone)
            theme_func(frame, intensity)
        except Exception:
            pass

    def _json(self, payload):
        return ("HTTP/1.1 200 OK\r\nContent-Type: application/json\r\n\r\n" + json.dumps(payload)).encode()

    def _parse(self, req):
        parts = req.split("\r\n\r\n", 1)
        if len(parts) < 2 or not parts[1]:
            return {}
        try:
            return json.loads(parts[1])
        except:
            return {}

    def _request(self, c):
        # Zorg dat de client-socket blokkerende mode heeft met timeout
        # zodat recv() niet direct EAGAIN gooit op non-blocking sockets.
        try:
            c.settimeout(3)
        except Exception:
            pass
        data = b""
        while b"\r\n\r\n" not in data and len(data) < 4096:
            try:
                ch = c.recv(512)
            except OSError:
                break
            if not ch:
                break
            data += ch
        if b"\r\n\r\n" in data:
            h, b = data.split(b"\r\n\r\n", 1)
            cl = 0
            for line in h.split(b"\r\n"):
                if line.lower().startswith(b"content-length:"):
                    try:
                        cl = int(line.split(b":", 1)[1].strip())
                    except:
                        cl = 0
            while len(b) < cl and len(data) < 8192:
                try:
                    ch = c.recv(min(512, cl - len(b)))
                except OSError:
                    break
                if not ch:
                    break
                data += ch
                b += ch
        return data.decode("utf-8", "ignore")

    def _serve_simple(self, c):
        try:
            c.settimeout(0.2)
        except:
            pass
        try:
            c.recv(256)
        except:
            pass
        ip = self.wifi.get_ip() if (self.wifi and self.wifi.is_connected()) else "offline"
        body = "ESP32 Alarm web alive\nip={}\n".format(ip)
        resp = "HTTP/1.1 200 OK\r\nContent-Type: text/plain\r\nConnection: close\r\n\r\n" + body
        c.send(resp.encode())

    def _weekday_name(self, idx):
        names = ("Maandag", "Dinsdag", "Woensdag", "Donderdag", "Vrijdag", "Zaterdag", "Zondag")
        return names[(int(idx) - 1) % 7]

    def _weekday_short(self, idx):
        names = ("ma", "di", "wo", "do", "vr", "za", "zo")
        return names[(int(idx) - 1) % 7]

    def _next_alarm_info(self, t):
        # Returns (day_str, hh, mm) for next alarm, or None if none
        # t[6] is weekday: 1=Mon ... 7=Sun, DAY_KEYS = ("mon","tue","wed","thu","fri","sat","sun")
        day_abbr = ("ma", "di", "wo", "do", "vr", "za", "zo")
        day_keys = ("mon", "tue", "wed", "thu", "fri", "sat", "sun")
        cfg = self.alarm_schedule
        if not isinstance(cfg, dict):
            return None
        today_idx = (int(t[6]) - 1) % 7  # 0=Mon
        cur_h = int(t[3])
        cur_m = int(t[4])
        for offset in range(7):
            di = (today_idx + offset) % 7
            key = day_keys[di]
            alarm = cfg.get(key)
            if alarm is None:
                continue
            enabled = alarm.get("enabled", False)
            if not enabled:
                continue
            try:
                hh = int(alarm.get("hour", 0))
                mm = int(alarm.get("minute", 0))
            except Exception:
                continue
            if offset == 0:
                # today: only if alarm time is still in future
                if hh > cur_h or (hh == cur_h and mm > cur_m):
                    return ("", hh, mm)
            else:
                return (day_abbr[di], hh, mm)
        return None

    def _draw_alarm_icon(self, x, y):
        # 8x8 pixel alarm bell icon
        pixels = (
            0b00010000,
            0b00111000,
            0b00111000,
            0b01111100,
            0b01111100,
            0b11111110,
            0b00010000,
            0b00111000,
        )
        for row, bits in enumerate(pixels):
            for col in range(8):
                if bits & (0x80 >> col):
                    self.display.pixel(x + col, y + row, 1)

    def _draw_big_char(self, ch, x, y, scale=3):
        glyph = BIG_TIME_GLYPHS.get(ch)
        if not glyph:
            return 0
        w = len(glyph[0]) if glyph else 0
        for row_idx, row in enumerate(glyph):
            for col_idx, bit in enumerate(row):
                if bit == "1":
                    self.display.fill_rect(x + col_idx * scale, y + row_idx * scale, scale, scale, 1)
        return (w * scale) + scale

    def _draw_big_time(self, hh, mm, y_offset=0):
        text = "{:02d}:{:02d}".format(hh, mm)
        max_height = 36  # Keep room for alarm + date lines below.
        scale = 1
        width = 0

        for cand in range(8, 0, -1):
            cand_width = 0
            for ch in text:
                glyph = BIG_TIME_GLYPHS.get(ch)
                if glyph:
                    cand_width += (len(glyph[0]) * cand) + cand
            cand_width = max(0, cand_width - cand)
            if cand_width <= WIDTH and (5 * cand) <= max_height:
                scale = cand
                width = cand_width
                break

        x = max(0, (WIDTH - width) // 2)
        y = y_offset + max(0, (max_height - (5 * scale)) // 2)
        for ch in text:
            x += self._draw_big_char(ch, x, y, scale)

    def _play_boot_intro(self):
        """8-bit retro boot intro: RETRO slaat neer van boven, GEORGY van onder.
        LED strip doet mee; 999.mp3 speelt op achtergrond.
        WiFi is al verbonden (gedaan in __init__).
        """
        if self.display is None:
            return
        self._in_intro = True
        self._skip_intro = False  # reset voor elke boot

        # ── Helper: teken tekst 2× geschaald (via tijdelijk framebuf) ────────
        def draw_2x(text, x, y, col=1):
            w = len(text) * 8
            rb = (w + 7) // 8
            buf = bytearray(rb * 8)
            fb = framebuf.FrameBuffer(buf, w, 8, framebuf.MONO_HLSB)
            fb.fill(0)
            fb.text(text, 0, 0, 1)
            for ty in range(8):
                for tx in range(w):
                    if fb.pixel(tx, ty):
                        self.display.fill_rect(x + tx * 2, y + ty * 2, 2, 2, col)

        # ── Helper: spat-pixels (puin) ───────────────────────────────────────
        def debris(seed, y_impact, count=12):
            for i in range(count):
                px = (seed * 17 + i * 37) % 124 + 2
                py = max(0, min(63, y_impact + (i * 7 % 8) - 3))
                self.display.pixel(px, py, 1)

        # ── LED helpers ──────────────────────────────────────────────────────
        def leds_set(r, g, b):
            if self.leds:
                self.leds.set_all(r, g, b)
                self.leds.show()

        def leds_clear():
            if self.leds:
                self.leds.clear()

        def leds_sweep_l2r(fi, r, g, b):
            """Sweep links→rechts: fi = frame (0..n_leds)."""
            if self.leds:
                n = self.leds.num_leds
                for i in range(n):
                    if i <= fi:
                        self.leds.set_pixel(i, r, g, b)
                    else:
                        self.leds.set_pixel(i, 0, 0, 0)
                self.leds.show()

        def leds_sweep_r2l(fi, r, g, b):
            """Sweep rechts→links: fi = frame (0..n_leds)."""
            if self.leds:
                n = self.leds.num_leds
                for i in range(n):
                    if i >= (n - 1 - fi):
                        self.leds.set_pixel(i, r, g, b)
                    else:
                        self.leds.set_pixel(i, 0, 0, 0)
                self.leds.show()

        def leds_rainbow(phase):
            if self.leds:
                n = self.leds.num_leds
                for i in range(n):
                    h = (phase * 12 + i * (256 // n)) % 256
                    s = h // 43
                    f = h % 43
                    p = 0
                    q = int(255 * (42 - f) // 42)
                    t = int(255 * f // 42)
                    if   s == 0: r2, g2, b2 = 255, t, p
                    elif s == 1: r2, g2, b2 = q, 255, p
                    elif s == 2: r2, g2, b2 = p, 255, t
                    elif s == 3: r2, g2, b2 = p, q, 255
                    elif s == 4: r2, g2, b2 = t, p, 255
                    else:        r2, g2, b2 = 255, p, q
                    self.leds.set_pixel(i, r2, g2, b2)
                self.leds.show()

        def leds_flicker(seed):
            cols = [(255,0,0),(255,80,0),(255,255,0),(0,255,0),(0,200,255),(80,0,255),(255,0,200)]
            if self.leds:
                n = self.leds.num_leds
                for i in range(n):
                    c = cols[(seed * 13 + i * 37) % len(cols)]
                    self.leds.set_pixel(i, c[0], c[1], c[2])
                self.leds.show()

        # ── Toon bootscherm terwijl DFPlayer opstart (blokkerende ~1.2s init) ──
        if self.display:
            self.display.fill(0)
            # "LOADING..." met pixel-ruis terwijl DFPlayer init blokt
            for i in range(30):
                px = (time.ticks_ms() * 13 + i * 37) % 128
                py = (time.ticks_ms() * 7  + i * 19) % 64
                self.display.pixel(px, py, 1)
            self.display.text("RETRO GEORGY", 8, 28, 1)
            self.display.text("loading...", 24, 42, 1)
            self.display.show()

        # DFPlayer initialiseren en track 999 afspelen
        try:
            if self._ensure_dfplayer_ready() and self.dfplayer is not None:
                self.dfplayer.set_volume(20)
                self.dfplayer.play_mp3(1)
                self._intro_audio_playing = True
                print("♫ Intro: 0001.mp3 afspelen")
        except Exception as _e:
            print("! Intro DFPlayer:", _e)

        # ── Layout constanten ────────────────────────────────────────────────
        # "RETRO"  = 5 chars × 8 × 2 = 80px breed  →  x=24 (gecentreerd)
        # "GEORGY" = 6 chars × 8 × 2 = 96px breed  →  x=16
        RETRO_X      = (128 - 5 * 8 * 2) // 2   # 24
        GEORGY_X     = (128 - 6 * 8 * 2) // 2   # 16
        RETRO_Y_END  = 2
        GEORGY_Y_END = 24

        # Slide-in keyframes (y-positie per frame)
        RETRO_YS  = [-16, -12, -6, -2, 2, 2, 2, 2]   # 8 frames
        GEORGY_YS = [ 64,  57,  48, 38, 30, 26, 24, 24]  # 8 frames

        # ── FASE 1: pixel-ruis + LED flikkeren (5 frames) ───────────────────
        for f in range(5):
            if self._skip_intro: break
            self.display.fill(0)
            seed = time.ticks_ms()
            for i in range(25):
                self.display.pixel((seed * 13 + i * 41) % 128, (seed * 7 + i * 23) % 64, 1)
            self.display.show()
            leds_flicker(seed + f)
            time.sleep_ms(50)

        # ── FASE 2: "RETRO" schuift neer van boven (8 frames) ───────────────
        for fi, ry in enumerate(RETRO_YS):
            if self._skip_intro: break
            self.display.fill(0)
            if ry > -16:
                draw_2x("RETRO", RETRO_X, ry, 1)
            # Motion trail: stippellijn net boven de tekst
            if fi > 0 and RETRO_YS[fi - 1] < ry:
                trail_y = max(0, ry - 3)
                self.display.hline(RETRO_X, trail_y, 80, 1)
            self.display.show()
            leds_sweep_l2r(fi, 255, 90 + fi * 20, 0)   # oranje sweep
            time.sleep_ms(50)

        # ── FASE 3: RETRO IMPACT (3 frames) ─────────────────────────────────
        for fi in range(3):
            if self._skip_intro: break
            self.display.fill(0)
            draw_2x("RETRO", RETRO_X, RETRO_Y_END, 1)
            impact_y = RETRO_Y_END + 17
            if fi == 0:
                # Dubbele shockwave lijn
                self.display.hline(0, impact_y,     128, 1)
                self.display.hline(0, impact_y + 1, 128, 1)
                debris(time.ticks_ms(), impact_y + 2)
            elif fi == 1:
                self.display.hline(0, impact_y + 2, 128, 1)
                debris(time.ticks_ms() + 11, impact_y + 1, 7)
            # fi==2: kalmeer
            self.display.show()
            leds_set(255, 120, 0)   # oranje flash
            time.sleep_ms(65)

        # ── FASE 4: "GEORGY" schuift op van onder (8 frames) ────────────────
        for fi, gy in enumerate(GEORGY_YS):
            if self._skip_intro: break
            self.display.fill(0)
            draw_2x("RETRO", RETRO_X, RETRO_Y_END, 1)
            if gy < 64:
                draw_2x("GEORGY", GEORGY_X, gy, 1)
            # Motion trail net onder de tekst
            if fi > 0 and GEORGY_YS[fi - 1] > gy:
                trail_y = min(63, gy + 17)
                self.display.hline(GEORGY_X, trail_y, 96, 1)
            self.display.show()
            leds_sweep_r2l(fi, 0, 200, 255)   # cyaan sweep
            time.sleep_ms(50)

        # ── FASE 5: GEORGY IMPACT (3 frames) ────────────────────────────────
        for fi in range(3):
            if self._skip_intro: break
            self.display.fill(0)
            draw_2x("RETRO",  RETRO_X,  RETRO_Y_END,  1)
            draw_2x("GEORGY", GEORGY_X, GEORGY_Y_END, 1)
            impact_y = GEORGY_Y_END - 2
            if fi == 0:
                self.display.hline(0, max(0, impact_y - 1), 128, 1)
                self.display.hline(0, max(0, impact_y - 2), 128, 1)
                debris(time.ticks_ms(), impact_y - 3, 10)
            elif fi == 1:
                self.display.hline(0, max(0, impact_y - 3), 128, 1)
                debris(time.ticks_ms() + 9, impact_y - 2, 6)
            self.display.show()
            leds_set(0, 200, 255)   # cyaan flash
            time.sleep_ms(65)

        # ── FASE 6: pixel-border + "ALARM KLOK" typt in (14 frames) ────────
        ALARMKLOK = "ALARM KLOK"
        ALARMKLOK_X = (128 - len(ALARMKLOK) * 8) // 2  # 4
        for fi in range(14):
            if self._skip_intro: break
            self.display.fill(0)
            draw_2x("RETRO",  RETRO_X,  RETRO_Y_END,  1)
            draw_2x("GEORGY", GEORGY_X, GEORGY_Y_END, 1)
            # Pixel-rand
            self.display.rect(0, 0, 128, 64, 1)
            self.display.rect(2, 2, 124, 60, 1)
            # Typ-effect: 1 extra teken per frame
            shown = min(len(ALARMKLOK), fi + 1)
            self.display.text(ALARMKLOK[:shown], ALARMKLOK_X, 50, 1)
            # Blinkende cursor
            if fi % 2 == 0 and shown < len(ALARMKLOK):
                self.display.text("_", ALARMKLOK_X + shown * 8, 50, 1)
            self.display.show()
            leds_rainbow(fi * 2)
            time.sleep_ms(70)

        # ── FASE 7: WiFi zoekt verbinding (animatie, 8-bit stijl) ───────────
        # 8-bit WiFi-icoon: 3 concentrische bogen + stip (16×10 px)
        def draw_wifi_icon(x, y, rings=3, invert=False):
            """Teken WiFi-icoon met 'rings' actieve bogen (0-3)."""
            d = self.display
            col = 0 if invert else 1
            # Stip (antenne-punt)
            d.fill_rect(x + 7, y + 9, 2, 2, col)
            # Boog 1 (klein)
            if rings >= 1:
                d.pixel(x + 5, y + 7, col); d.pixel(x + 6, y + 6, col)
                d.pixel(x + 9, y + 6, col); d.pixel(x + 10, y + 7, col)
            # Boog 2 (middel)
            if rings >= 2:
                d.pixel(x + 3, y + 6, col); d.pixel(x + 4, y + 5, col)
                d.pixel(x + 5, y + 4, col); d.pixel(x + 6, y + 3, col)
                d.pixel(x + 9, y + 3, col); d.pixel(x + 10, y + 4, col)
                d.pixel(x + 11, y + 5, col); d.pixel(x + 12, y + 6, col)
            # Boog 3 (groot)
            if rings >= 3:
                d.pixel(x + 1, y + 6, col); d.pixel(x + 2, y + 4, col)
                d.pixel(x + 3, y + 2, col); d.pixel(x + 4, y + 1, col)
                d.pixel(x + 6, y,     col); d.pixel(x + 9, y,     col)
                d.pixel(x + 11, y + 1, col); d.pixel(x + 12, y + 2, col)
                d.pixel(x + 13, y + 4, col); d.pixel(x + 14, y + 6, col)

        WIFI_X = (128 - 16) // 2   # gecentreerd
        WIFI_Y = 28
        SCAN_TEXT = "SCANNING..."
        SCAN_X = (128 - len(SCAN_TEXT) * 8) // 2

        for fi in range(24):
            if self._skip_intro: break
            self.display.fill(0)
            # Titel bovenaan (klein)
            self.display.text("RETRO GEORGY", 8, 2, 1)
            self.display.hline(0, 11, 128, 1)
            # Pulserende bogen: cyclus 0→1→2→3→2→1→0...
            pulse = fi % 8
            rings = pulse if pulse <= 3 else (6 - pulse)
            draw_wifi_icon(WIFI_X, WIFI_Y, rings)
            # Knipperende scan-tekst
            if fi % 4 < 3:
                self.display.text(SCAN_TEXT, SCAN_X, 52, 1)
            # Voortgangspuntjes onder het icoon
            dots = fi % 4
            for d2 in range(dots + 1):
                self.display.fill_rect(52 + d2 * 8, 42, 4, 4, 1)
            self.display.show()
            leds_sweep_l2r(fi % 8, 0, 180, 255)
            time.sleep_ms(80)

        # ── FASE 8: BAM! IP-adres gevonden ──────────────────────────────────
        ip = self.wifi.get_ip() if (self.wifi_ok and self.wifi) else None

        if self._skip_intro:
            self.startup_ip_until = None
            leds_clear()
            try:
                if self.dfplayer:
                    self.dfplayer.stop()
            except Exception:
                pass
            self._intro_audio_playing = False
            self._in_intro = False
            return

        def _safe_ascii_text(value, max_chars=16):
            try:
                s = str(value if value is not None else "")
            except Exception:
                s = ""
            out = []
            for ch in s:
                code = ord(ch)
                if 32 <= code <= 126:
                    out.append(ch)
                else:
                    out.append("?")
            if not out:
                out = ["-"]
            txt = "".join(out)
            if len(txt) > max_chars:
                return txt[:max_chars]
            return txt

        try:
            # BAM flash: 3 frames wit knippert
            for fi in range(3):
                if self._skip_intro:
                    break
                self.display.fill(fi % 2)
                if fi % 2 == 0:
                    self.display.text("  ** BAM! **  ", 0, 26, 1)
                self.display.show()
                leds_set(255, 255, 0)
                time.sleep_ms(80)

            # Lange WiFi reveal (zelfde gevoel/duur), maar geheugen-zuinig getekend.
            GEVONDEN = "GEVONDEN!"
            SSID_LABEL = "VERBONDEN MET"
            IP_LABEL = "IP ADRES"
            ssid_str = _safe_ascii_text(self.wifi_ssid or "onbekend", max_chars=16)
            ip_str = _safe_ascii_text(ip if ip else "geen WiFi", max_chars=16)

            def _draw_typed(text, shown, x, y):
                count = shown if shown < len(text) else len(text)
                i = 0
                while i < count:
                    self.display.text(text[i], x + i * 8, y, 1)
                    i += 1

            total_frames = len(GEVONDEN) + len(SSID_LABEL) + len(ssid_str) + len(IP_LABEL) + len(ip_str) + 20
            for fi in range(total_frames):
                if self._skip_intro:
                    break

                self.display.fill(0)
                self.display.text("RETRO GEORGY", 8, 2, 1)
                self.display.hline(0, 11, 128, 1)
                draw_wifi_icon(2, 18, 3)

                g_shown = fi + 1
                _draw_typed(GEVONDEN, g_shown, 24, 18)
                if fi < len(GEVONDEN) and (fi % 2 == 0):
                    cursor_x = 24 + (g_shown if g_shown < len(GEVONDEN) else len(GEVONDEN)) * 8
                    self.display.text("_", cursor_x, 18, 1)

                ssid_label_fi = fi - len(GEVONDEN) - 1
                if ssid_label_fi >= 0:
                    _draw_typed(SSID_LABEL, ssid_label_fi + 1, 0, 30)

                ssid_text_fi = fi - len(GEVONDEN) - len(SSID_LABEL) - 2
                if ssid_text_fi >= 0:
                    _draw_typed(ssid_str, ssid_text_fi + 1, 0, 38)
                    if ssid_text_fi < len(ssid_str) and (ssid_text_fi % 2 == 0):
                        cursor_x = (ssid_text_fi + 1 if (ssid_text_fi + 1) < len(ssid_str) else len(ssid_str)) * 8
                        self.display.text("_", cursor_x, 38, 1)

                ip_label_fi = fi - len(GEVONDEN) - len(SSID_LABEL) - len(ssid_str) - 3
                if ip_label_fi >= 0:
                    _draw_typed(IP_LABEL, ip_label_fi + 1, 0, 48)

                ip_text_fi = fi - len(GEVONDEN) - len(SSID_LABEL) - len(ssid_str) - len(IP_LABEL) - 4
                if ip_text_fi >= 0:
                    _draw_typed(ip_str, ip_text_fi + 1, 0, 56)
                    if ip_text_fi < len(ip_str) and (ip_text_fi % 2 == 0):
                        cursor_x = (ip_text_fi + 1 if (ip_text_fi + 1) < len(ip_str) else len(ip_str)) * 8
                        self.display.text("_", cursor_x, 56, 1)

                if fi >= (total_frames - 16):
                    if (fi % 4) < 2:
                        self.display.rect(0, 12, 128, 52, 1)

                self.display.show()
                leds_rainbow(40 + fi * 4)
                if (fi % 10) == 0:
                    gc.collect()
                time.sleep_ms(70)

            # Vasthouden (zelfde duur als eerder, ca. 1.5s)
            for fi in range(18):
                if self._skip_intro:
                    break
                self.display.fill(0)
                self.display.text("RETRO GEORGY", 8, 2, 1)
                self.display.hline(0, 11, 128, 1)
                draw_wifi_icon(2, 18, 3)
                self.display.text(GEVONDEN, 24, 18, 1)
                self.display.text(SSID_LABEL, 0, 30, 1)
                self.display.text(ssid_str, 0, 38, 1)
                self.display.text(IP_LABEL, 0, 48, 1)
                self.display.text(ip_str, 0, 56, 1)
                self.display.rect(0, 12, 128, 52, 1)
                self.display.show()
                leds_rainbow(110 + fi * 3)
                if (fi % 6) == 0:
                    gc.collect()
                time.sleep_ms(80)
        except Exception as _e:
            # Intro mag de hoofdloop nooit blokkeren.
            print("! Intro WiFi reveal fout:", _e)

        # Zet startup_ip_until op None: IP al getoond in intro
        self.startup_ip_until = None

        leds_clear()
        self._intro_audio_playing = False
        self._in_intro = False
        gc.collect()
        print("Boot intro klaar")

    def _draw_startup_ip(self):
        self.display.fill(0)
        self.display.text("WiFi verbonden", 8, 8, 1)
        ip = self.wifi.get_ip() if self.wifi_ok else None
        self.display.text("IP adres:", 8, 26, 1)
        self.display.text(ip if ip else "geen netwerk", 8, 40, 1)
        self.display.show()

    def _draw_wifi_intro_style_icon(self, x, y, rings=3):
        # Zelfde 8-bit stijl als in de boot-intro (16x10).
        d = self.display
        # Stip (antenne-punt)
        d.fill_rect(x + 7, y + 9, 2, 2, 1)
        # Boog 1 (klein)
        if rings >= 1:
            d.pixel(x + 5, y + 7, 1); d.pixel(x + 6, y + 6, 1)
            d.pixel(x + 9, y + 6, 1); d.pixel(x + 10, y + 7, 1)
        # Boog 2 (middel)
        if rings >= 2:
            d.pixel(x + 3, y + 6, 1); d.pixel(x + 4, y + 5, 1)
            d.pixel(x + 5, y + 4, 1); d.pixel(x + 6, y + 3, 1)
            d.pixel(x + 9, y + 3, 1); d.pixel(x + 10, y + 4, 1)
            d.pixel(x + 11, y + 5, 1); d.pixel(x + 12, y + 6, 1)
        # Boog 3 (groot)
        if rings >= 3:
            d.pixel(x + 1, y + 6, 1); d.pixel(x + 2, y + 4, 1)
            d.pixel(x + 3, y + 2, 1); d.pixel(x + 4, y + 1, 1)
            d.pixel(x + 6, y, 1); d.pixel(x + 9, y, 1)
            d.pixel(x + 11, y + 1, 1); d.pixel(x + 12, y + 2, 1)
            d.pixel(x + 13, y + 4, 1); d.pixel(x + 14, y + 6, 1)

    def _draw_wifi_status_icon(self, x, y):
        self._draw_wifi_intro_style_icon(x, y, 3)

    def _draw_wifi_off_icon(self, x, y):
        self._draw_wifi_intro_style_icon(x, y, 3)
        # Streep er doorheen
        self.display.line(x + 1, y + 1, x + 14, y + 10, 1)

    def _fetch_weather(self):
        """Haal actueel weer op van Open-Meteo (plain HTTP, geen API-key)."""
        try:
            if self.config:
                lat = self.config.get("weather", "latitude", 51.92)
                lon = self.config.get("weather", "longitude", 6.08)
            else:
                lat, lon = 51.92, 6.08
            host = "api.open-meteo.com"
            path = "/v1/forecast?latitude={}&longitude={}&current=temperature_2m,weathercode".format(lat, lon)
            s = socket.socket()
            s.settimeout(8)
            addr = socket.getaddrinfo(host, 80)[0][-1]
            s.connect(addr)
            s.send("GET {} HTTP/1.0\r\nHost: {}\r\n\r\n".format(path, host).encode())
            resp = b""
            while True:
                chunk = s.recv(256)
                if not chunk:
                    break
                resp += chunk
            s.close()
            # Zoek JSON-body na dubbele newline
            idx = resp.find(b"\r\n\r\n")
            if idx < 0:
                return
            body = resp[idx + 4:].decode()
            # Parseer temperature_2m en weathercode zonder json.loads (RAM-zuinig)
            def _extract(key, text):
                i = text.find('"' + key + '"')
                if i < 0:
                    return None
                i = text.find(":", i) + 1
                while i < len(text) and text[i] in " \t":
                    i += 1
                j = i
                while j < len(text) and text[j] not in ",}":
                    j += 1
                try:
                    return float(text[i:j])
                except Exception:
                    return None
            # Zoek alleen in het "current"-blok
            ci = body.find('"current"')
            block = body[ci:ci + 200] if ci >= 0 else body
            temp = _extract("temperature_2m", block)
            code = _extract("weathercode", block)
            if temp is not None:
                self._weather_temp = int(temp + 0.5)
            if code is not None:
                self._weather_code = int(code)
            gc.collect()
        except Exception as e:
            print("! Weer ophalen mislukt:", e)

    def _url_quote(self, value):
        text = str(value or "")
        if quote is not None:
            try:
                return quote(text)
            except Exception:
                pass
        safe = []
        for ch in text:
            code = ord(ch)
            if (48 <= code <= 57) or (65 <= code <= 90) or (97 <= code <= 122) or ch in "-_.~":
                safe.append(ch)
            elif ch == " ":
                safe.append("%20")
            else:
                safe.append("%%%02X" % code)
        return "".join(safe)

    def _resolve_weather_location(self, place_name):
        """Zoek plaatsnaam op via Open-Meteo geocoding API en geef beste match terug."""
        host = "geocoding-api.open-meteo.com"
        encoded = self._url_quote(place_name)
        path = "/v1/search?name={}&count=1&language=nl&format=json".format(encoded)
        s = socket.socket()
        try:
            s.settimeout(8)
            addr = socket.getaddrinfo(host, 80)[0][-1]
            s.connect(addr)
            s.send((
                "GET {} HTTP/1.0\r\n"
                "Host: {}\r\n\r\n"
            ).format(path, host).encode())
            resp = b""
            while True:
                chunk = s.recv(256)
                if not chunk:
                    break
                resp += chunk
        finally:
            try:
                s.close()
            except Exception:
                pass

        idx = resp.find(b"\r\n\r\n")
        if idx < 0:
            raise ValueError("Geen geldig antwoord van geocoding")
        payload = json.loads(resp[idx + 4:].decode())
        results = payload.get("results") or []
        if not results:
            raise ValueError("Plaats niet gevonden")

        best = results[0]
        resolved_name = best.get("name") or str(place_name)
        admin1 = best.get("admin1")
        country = best.get("country")
        parts = [resolved_name]
        if admin1 and admin1 != resolved_name:
            parts.append(admin1)
        if country:
            parts.append(country)

        return {
            "place": ", ".join(parts),
            "latitude": float(best.get("latitude")),
            "longitude": float(best.get("longitude")),
        }

    def _check_weather_fetch(self):
        """Roep dit aan vanuit de main loop. Zet WiFi tijdelijk aan als nodig."""
        if not self.config or not self.config.get("weather", "enabled", True):
            return
        now_ms = time.ticks_ms()
        if time.ticks_diff(now_ms, self._weather_next_ms) < 0:
            return
        # Nog binnen de 30-min opstart-WiFi-window? Dan gewoon fetchen.
        # Anders: WiFi tijdelijk aanzetten, fetchen, weer uitzetten.
        wifi_was_disabled = self.wifi_disabled
        if wifi_was_disabled:
            print("Weer ophalen: WiFi tijdelijk aan")
            self.wifi_disabled = False
            self._ensure_wifi_connected()
        if self.wifi_ok and self.wifi and self.wifi.is_connected():
            self._fetch_weather()
            self._weather_next_ms = time.ticks_add(now_ms, self._weather_interval_ms)
            print("Weer opgehaald: {}C code {}".format(self._weather_temp, self._weather_code))
        else:
            # Mislukt: 10 min later opnieuw proberen
            self._weather_next_ms = time.ticks_add(now_ms, 10 * 60 * 1000)
        if wifi_was_disabled:
            self._disable_wifi()
            self.wifi_disabled = True
            print("Weer ophalen klaar: WiFi weer uit")

    def _draw_weather_overlay(self, t):
        now_ms = time.ticks_ms()
        # DS3231 temperatuur ophalen (elke 60s, gecached) als fallback
        if self.clock.rtc is not None and time.ticks_diff(now_ms, self._rtc_temp_next_ms) >= 0:
            try:
                self._rtc_temp = self.clock.rtc.temperature()
                self._rtc_temp_next_ms = time.ticks_add(now_ms, 60000)
            except Exception:
                pass

        wifi_up = self.wifi_ok and self.wifi and self.wifi.is_connected()
        # Temperatuur tonen: buitentemperatuur als beschikbaar, anders DS3231
        disp_temp = self._weather_temp if self._weather_temp is not None else (
            int(self._rtc_temp + 0.5) if self._rtc_temp is not None else None)
        if disp_temp is not None:
            temp_str = "{}C".format(disp_temp)
            self.display.text(temp_str, 96 - len(temp_str) * 8 - 2, 56, 1)

        x, y = 96, 56
        h = int(t[3])
        self._weather_phase = (self._weather_phase + 1) % 20

        # Nacht: maan + sterren (ongeacht weercode)
        if h >= 20 or h < 6:
            self.display.fill_rect(x, y, 8, 8, 0)
            self.display.fill_rect(x + 1, y + 1, 4, 4, 1)
            self.display.fill_rect(x + 3, y + 1, 3, 4, 0)
            if self._weather_phase % 4 == 0:
                self.display.pixel(x + 7, y + 1, 1)
                self.display.pixel(x + 6, y + 5, 1)
            return

        # WMO-code → icoon (0-3=helder, 45-48=mist, 51-67/80-82=regen, 71-77=sneeuw, 95-99=onweer)
        code = self._weather_code
        if code is None:
            # Geen data: RSSI-fallback
            try:
                rssi = self.wifi.sta.status('rssi') if wifi_up else -80
            except Exception:
                rssi = -80
            code = 0 if rssi >= -67 else (3 if rssi >= -78 else 61)

        if code <= 3:
            # Zon / weinig bewolkt
            self.display.fill_rect(x + 2, y + 2, 4, 4, 1)
            self.display.pixel(x + 4, y, 1)
            self.display.pixel(x + 4, y + 7, 1)
            self.display.pixel(x, y + 4, 1)
            self.display.pixel(x + 7, y + 4, 1)
        elif code <= 48:
            # Bewolkt / mist
            self.display.hline(x, y + 2, 8, 1)
            self.display.hline(x - 1, y + 4, 10, 1)
            self.display.hline(x, y + 6, 8, 1)
        elif code <= 67 or (80 <= code <= 82):
            # Regen
            self.display.hline(x, y + 2, 8, 1)
            self.display.hline(x - 1, y + 4, 10, 1)
            self.display.hline(x, y + 6, 8, 1)
            if self._weather_phase % 3 == 0:
                self.display.pixel(x + 2, y + 7, 1)
                self.display.pixel(x + 5, y + 7, 1)
        elif code <= 77:
            # Sneeuw: wolkje + stipjes
            self.display.hline(x, y + 2, 8, 1)
            self.display.hline(x - 1, y + 4, 10, 1)
            if self._weather_phase % 2 == 0:
                self.display.pixel(x + 1, y + 6, 1)
                self.display.pixel(x + 4, y + 7, 1)
                self.display.pixel(x + 7, y + 6, 1)
        else:
            # Onweer: wolkje + bliksem
            self.display.hline(x, y + 2, 8, 1)
            self.display.hline(x - 1, y + 4, 10, 1)
            self.display.hline(x, y + 6, 8, 1)
            if self._weather_phase % 4 < 2:
                self.display.pixel(x + 4, y + 7, 1)

    def _update_easter_egg(self, t):
        hh = int(t[3])
        mm = int(t[4])
        ss = int(t[5])
        key = hh * 100 + mm
        secret = {
            707: "LUCKY 707",
            1337: "LEET MODE",
            2121: "RETRO PORTAL",
        }
        if ss == 0 and key in secret and self._easter_key != (key, int(t[2]), int(t[1])):
            self._easter_key = (key, int(t[2]), int(t[1]))
            self._easter_message = secret[key]
            self._easter_active_until = time.ticks_add(time.ticks_ms(), 5000)

    def _draw_easter_overlay(self):
        if self._easter_active_until is None:
            return
        if time.ticks_diff(self._easter_active_until, time.ticks_ms()) <= 0:
            self._easter_active_until = None
            self._easter_message = ""
            return
        self.display.fill_rect(0, 0, 128, 10, 1)
        self.display.text(self._easter_message[:18], 4, 1, 0)

    def _apply_display_brightness(self, force=False):
        if not self.display:
            return
        boss = self._alarm_boss_level() > 0
        # Stabiele helderheid: geen automatische dag/nacht-wissel.
        state = ("boss", self._display_manual_mode) if boss else ("steady", self._display_manual_mode)
        if (not force) and state == self._display_dim_state:
            return
        self._display_dim_state = state
        try:
            self.display.write_cmd(0x81)
            if boss:
                self.display.write_cmd(0xCF)
            else:
                # Alleen handmatige standen, zonder automatische tijdsafhankelijke puls/wissel.
                values = (0xCF, 0x2A, 0x05)
                self.display.write_cmd(values[self._display_manual_mode])
        except Exception:
            pass

    def _apply_clock_dither(self, t):
        # Dither uitgeschakeld: voorkomt zichtbaar flikkeren/ademen op sommige OLED panelen.
        return

    def _draw_clock_layout(self):
        t = self.clock.read_time()
        cur_hour = int(t[3])

        # ── Eerste keer (geen IP-scherm gehad): boot-transitie met LEDs ─────
        if self._transition_pending and not self._transition_active:
            self._transition_pending = False
            self._last_hour_shown = cur_hour
            self._start_clock_transition(use_leds=True)

        # ── Uur-omslag detectie: GEEN LEDs (niet 's nachts storen) ───────────
        if self._last_hour_shown != -1 and cur_hour != self._last_hour_shown:
            if not self._transition_active:
                self._start_clock_transition(use_leds=False)
        self._last_hour_shown = cur_hour

        # Als transitie bezig: animatie afhandelen in plaats van directe render
        if self._transition_active:
            done = self._step_clock_transition()
            if done:
                self._transition_active = False
                self._transition_buf = None
                if self.leds:
                    try:
                        if self._nightlight_on:
                            for i in range(self.leds.num_leds):
                                self.leds.set_pixel(i, 255, 120, 40)
                            self.leds.show()
                        else:
                            self.leds.clear()
                    except Exception:
                        pass
                gc.collect()
            return

        self._update_easter_egg(t)
        # Nachtlampje bijhouden buiten transitie/alarm
        if self.leds and self._nightlight_on and self.alarm_until is None:
            try:
                for i in range(self.leds.num_leds):
                    self.leds.set_pixel(i, 255, 120, 40)
                self.leds.show()
            except Exception:
                pass
        self.display.fill(0)
        self._draw_big_time(t[3], t[4])
        # Alarmregel: normaal het eerstvolgende alarm, maar tijdens snooze een countdown.
        snooze_sec = self._snooze_remaining_seconds()
        if snooze_sec > 0:
            sh = snooze_sec // 3600
            sm = (snooze_sec % 3600) // 60
            ss = snooze_sec % 60
            self.display.text("SNOOZE {:02d}:{:02d}:{:02d}".format(sh, sm, ss), 0, 44, 1)
        else:
            next_alarm = self._next_alarm_info(t)
            if next_alarm:
                day_str, ah, am = next_alarm
                if not day_str:
                    day_str = self._weekday_short(t[6])  # vandaag, nog in de toekomst
                alarm_text = "{} {:02d}:{:02d}".format(day_str, ah, am)
                self._draw_alarm_icon(0, 44)
                self.display.text(alarm_text, 10, 44, 1)
            else:
                self.display.text("--:--", 10, 44, 1)
        # Day + date lines
        self.display.text(self._weekday_short(t[6]), 0, 56, 1)
        self.display.text("{:02d}-{:02d}".format(t[2], t[1]), 24, 56, 1)
        self._draw_weather_overlay(t)
        if self.wifi_disabled:
            self._draw_wifi_off_icon(WIDTH - 16, HEIGHT - 11)
        elif self.wifi_ok and self.wifi and self.wifi.is_connected():
            self._draw_wifi_status_icon(WIDTH - 16, HEIGHT - 11)

        # Korte statusmelding na SET-kort in standaard scherm.
        now_ms = time.ticks_ms()
        if self._set_feedback_until and time.ticks_diff(self._set_feedback_until, now_ms) > 0:
            # Volledig scherm wissen en feedback tonen
            self.display.fill(0)
            lines = self._set_feedback_lines if self._set_feedback_lines else [self._set_feedback_text]
            y_positions = [2, 14, 26, 36, 48, 56]
            line_idx = 0
            y_idx = 0
            while line_idx < len(lines) and y_idx < len(y_positions):
                ln = lines[line_idx]
                if ln == "---":
                    self.display.hline(4, y_positions[y_idx] + 3, 120, 1)
                elif ln:
                    x = max(0, (128 - len(ln) * 8) // 2)
                    self.display.text(ln, x, y_positions[y_idx], 1)
                y_idx += 1
                line_idx += 1
        elif self._set_feedback_until:
            self._set_feedback_until = 0
            self._set_feedback_text = ""
            self._set_feedback_lines = []

        self._draw_easter_overlay()
        self._apply_clock_dither(t)
        self.display.show()

    # ═══════════════════════════════════════════════════════════════════════
    # Klok-scherm transitie animaties (5 varianten, random gekozen)
    # ═══════════════════════════════════════════════════════════════════════

    def _snapshot_clock(self):
        """Render het huidige klokscherm naar een losse bytearray buffer."""
        t = self.clock.read_time()
        old_buf = bytearray(self.display.buffer)   # bewaar huidig scherm
        self.display.fill(0)
        self._draw_big_time(t[3], t[4])
        next_alarm = self._next_alarm_info(t)
        if next_alarm:
            day_str, ah, am = next_alarm
            if not day_str:
                day_str = self._weekday_short(t[6])
            self._draw_alarm_icon(0, 44)
            self.display.text("{} {:02d}:{:02d}".format(day_str, ah, am), 10, 44, 1)
        else:
            self.display.text("--:--", 10, 44, 1)
        self.display.text(self._weekday_short(t[6]), 0, 56, 1)
        self.display.text("{:02d}-{:02d}".format(t[2], t[1]), 24, 56, 1)
        self._draw_weather_overlay(t)
        snapshot = bytearray(self.display.buffer)
        self.display.buffer[:] = old_buf   # herstel
        return snapshot

    def _buf_pixel(self, buf, x, y):
        """Lees pixel uit MONO_VLSB buffer (128×64)."""
        if x < 0 or x >= 128 or y < 0 or y >= 64:
            return 0
        page = y >> 3
        bit  = y & 7
        return 1 if (buf[page * 128 + x] >> bit) & 1 else 0

    def _start_clock_transition(self, use_leds=True):
        """Snapshot het doel-scherm, kies random methode, start animatie.
        use_leds=False bij uur-omslag (niet 's nachts storen).
        """
        try:
            self._transition_buf = self._snapshot_clock()
        except Exception:
            return
        self._transition_id   = (time.ticks_ms() // 7) % 5
        self._transition_step = 0
        self._transition_use_leds = use_leds
        self._transition_active = True

    def _pick_and_start_transition(self):
        """Voor opstart: zet pending-transitie om naar animatie."""
        if self._transition_pending:
            self._transition_pending = False
            self._start_clock_transition()

    def _step_clock_transition(self):
        """Voer één frame van de lopende transitie uit. Geeft True als klaar.
        Alle bewerkingen op page-niveau (byte slices) – geen pixel-for-loop.
        Buffer layout MONO_VLSB: buf[page*128 + x] = 8 verticale pixels op kolom x.
        """
        tid  = self._transition_id
        step = self._transition_step
        buf  = self._transition_buf
        d    = self.display

        # ── 0: Tetris – 4 banden (elk 16px = 2 pages) schuiven naar beneden ──
        if tid == 0:
            TOTAL = 28
            # band_start[i] = frame waarop band i begint te vallen
            band_start = (0, 5, 11, 17)
            d.fill(0)
            for band in range(4):
                p_final = band * 2          # doelpagina (0, 2, 4, 6)
                elapsed = step - band_start[band]
                if elapsed < 0:
                    continue
                elif elapsed >= 4:
                    # Geland: kopieer 2 pages direct uit snapshot (byte-slice)
                    for p in range(2):
                        so = (p_final + p) * 128
                        d.buffer[so:so+128] = buf[so:so+128]
                    # Impact-streep op frame van landing
                    if elapsed == 4:
                        d.hline(0, min(63, p_final * 8 + 16), 128, 1)
                else:
                    # Valt: verplaats pages 1 pagina per 1.5 frame omlaag
                    # elapsed 1→3: start 3,2,1 pages boven eindpositie
                    fall_pages_above = 3 - elapsed
                    for p in range(2):
                        src_o = (p_final + p) * 128
                        dst_page = p_final + p - fall_pages_above
                        if 0 <= dst_page < 8:
                            d.buffer[dst_page * 128 : dst_page * 128 + 128] = buf[src_o:src_o+128]
            if self._transition_use_leds and self.leds:
                cols = [(0,200,255),(255,200,0),(255,0,200),(0,255,80)]
                landed = sum(1 for bs in band_start if step >= bs + 4)
                col = cols[min(landed, 3)]
                n = self.leds.num_leds
                lit = max(1, step * n // TOTAL)
                for i in range(n):
                    self.leds.set_pixel(i, col[0] if i < lit else 0, col[1] if i < lit else 0, col[2] if i < lit else 0)
                self.leds.show()
            d.show()
            self._transition_step += 1
            return self._transition_step >= TOTAL

        # ── 1: Space Invaders scan – beam onthult L→R via page-slice ─────
        elif tid == 1:
            TOTAL = 24
            d.fill(0)
            beam_x = min(127, step * 6)
            # Kopieer kolommen 0..beam_x per page (byte-slice per rij)
            for page in range(8):
                base = page * 128
                d.buffer[base : base + beam_x] = buf[base : base + beam_x]
            # Beam: verticale stippellijn
            for y in range(0, 64, 3):
                d.pixel(beam_x, y, 1)
            # 3 invader-sprites (2×2 px pixels, klein gehouden)
            INV = (0b01100110, 0b11111111, 0b01111110, 0b00111100)
            for j in range(3):
                ix = (step * 3 + j * 30) % 138 - 10
                iy = 2 + j * 5
                for row, byte in enumerate(INV):
                    for bit in range(8):
                        if (byte >> (7 - bit)) & 1:
                            px2 = ix + bit
                            if 0 <= px2 < 128:
                                d.pixel(px2, iy + row, 1)
            if self._transition_use_leds and self.leds:
                n = self.leds.num_leds
                lit = step * n // TOTAL
                for i in range(n):
                    g = 220 if i == lit % n else (80 if i < lit else 0)
                    self.leds.set_pixel(i, 0, g, 0)
                self.leds.show()
            d.show()
            self._transition_step += 1
            return self._transition_step >= TOTAL

        # ── 2: Matrix regen – kolommen onthullen van boven naar beneden ───
        elif tid == 2:
            TOTAL = 32
            # 16 kolomgroepen van 8px; snelheid per groep (1, 2 of 3)
            col_speeds = (2,1,3,1,2,3,1,2,1,3,2,1,3,1,2,3)
            d.fill(0)
            for ci in range(16):
                cx = ci * 8
                pages_done = min(8, step * col_speeds[ci] // 5)
                # Kopieer onthulde pages via byte-slice
                for page in range(pages_done):
                    o = page * 128 + cx
                    d.buffer[o : o + 8] = buf[o : o + 8]
                # Regen-druppel net onder onthulde area
                if pages_done < 8:
                    drop_y = pages_done * 8 + (step % 8)
                    if drop_y < 64:
                        d.pixel(cx + (ci * 17) % 8, drop_y, 1)
            if self._transition_use_leds and self.leds:
                n = self.leds.num_leds
                lit = min(n, step * n // TOTAL)
                for i in range(n):
                    self.leds.set_pixel(i, 0, 200 if i < lit else 0, 0)
                self.leds.show()
            d.show()
            self._transition_step += 1
            return self._transition_step >= TOTAL

        # ── 3: Pac-Man – onthult L→R via page-slice, sprite erop getekend ─
        elif tid == 3:
            TOTAL = 26
            pac_x = min(128, step * 5)
            d.fill(0)
            # Kopieer kolommen links van Pac-Man via byte-slice
            reveal = min(pac_x, 128)
            for page in range(8):
                base = page * 128
                d.buffer[base : base + reveal] = buf[base : base + reveal]
            # Pac-Man sprite (12×12)
            px2 = min(pac_x, 116)
            py2 = 26
            mouth_open = (step % 4) < 2
            d.fill_rect(px2, py2, 12, 12, 1)
            for cx2, cy2 in ((px2, py2), (px2+11, py2), (px2, py2+11), (px2+11, py2+11)):
                d.pixel(cx2, cy2, 0)
            if mouth_open:
                d.fill_rect(px2+6, py2+2, 6, 8, 0)
                d.line(px2+6, py2+5, px2+11, py2+2, 0)
                d.line(px2+6, py2+6, px2+11, py2+9, 0)
            d.pixel(px2+4, py2+2, 0)
            if self._transition_use_leds and self.leds:
                n = self.leds.num_leds
                lit = min(n, step * n // TOTAL)
                ycol = (255, 220, 0) if (step % 4 < 2) else (255, 255, 80)
                for i in range(n):
                    self.leds.set_pixel(i, ycol[0] if i < lit else 0, ycol[1] if i < lit else 0, 0)
                self.leds.show()
            d.show()
            self._transition_step += 1
            return self._transition_step >= TOTAL

        # ── 4: CRT power-on – pages groeien open vanuit midden ────────────
        elif tid == 4:
            TOTAL = 28
            d.fill(0)
            if step < 14:
                # Fase 1: breid uit vanuit pagina 3-4 naar buiten (1 page per stap)
                half = step // 2 + 1
                p_start = max(0, 4 - half)
                p_end   = min(8, 4 + half)
                for page in range(p_start, p_end):
                    o = page * 128
                    d.buffer[o : o + 128] = buf[o : o + 128]
                # Gloed-lijn aan rand
                if p_start > 0:
                    d.hline(0, p_start * 8, 128, 1)
                if p_end < 8:
                    d.hline(0, min(63, p_end * 8 - 1), 128, 1)
            elif step < 22:
                # Fase 2: interlaced flicker – wissel even/oneven pages
                phase = (step - 14) % 2
                for page in range(phase, 8, 2):
                    o = page * 128
                    d.buffer[o : o + 128] = buf[o : o + 128]
            else:
                # Fase 3: volledig beeld via één buffer-copy
                d.buffer[:] = buf[:]
            if self._transition_use_leds and self.leds:
                n = self.leds.num_leds
                br = max(0, 220 - step * 8)
                for i in range(n):
                    self.leds.set_pixel(i, br, br, br)
                self.leds.show()
            d.show()
            self._transition_step += 1
            return self._transition_step >= TOTAL

        # Fallback
        return True


    def _draw_zelda_animation(self, frame):
        d = self.display
        d.fill(0)
        f = frame % 16
        H, S = 17, 10

        # Triforce: top apex (64,4), bl (54,21), br (74,21)
        def _tfill(ax, ay, c=1):
            for dy in range(H + 1):
                w = max(1, 2 * S * dy // H)
                d.hline(ax - w // 2, ay + dy, w, c)

        def _tline(ax, ay):
            d.line(ax, ay, ax - S, ay + H, 1)
            d.line(ax, ay, ax + S, ay + H, 1)
            d.hline(ax - S, ay + H, 2 * S + 1, 1)

        if f < 4:
            # BL+BR vast, Top knippert
            _tfill(54, 21); _tfill(74, 21)
            if f % 2 == 0:
                _tfill(64, 4)
            else:
                _tline(64, 4)
        elif f < 12:
            # Alle drie vol (langste fase)
            _tfill(64, 4); _tfill(54, 21); _tfill(74, 21)
        else:
            # Invert: wit vlak, zwarte triforce omtrekken
            d.fill_rect(43, 3, 42, 36, 1)
            d.line(64, 4, 54, 21, 0); d.line(64, 4, 74, 21, 0); d.hline(54, 21, 21, 0)
            d.line(54, 21, 44, 38, 0); d.line(54, 21, 64, 38, 0); d.hline(44, 38, 21, 0)
            d.line(74, 21, 64, 38, 0); d.line(74, 21, 84, 38, 0); d.hline(64, 38, 21, 0)

        # ZELDA tekst (x=44-84, gelijk met triforce)
        d.text("ZELDA", 44, 46, 1)

        # ALARM balk knippert
        if (frame // 10) % 2 == 0:
            d.fill_rect(0, 56, 128, 8, 1)
            d.text("ALARM!", 40, 56, 0)
        else:
            d.text("ALARM!", 40, 56, 1)

        # 3 hartjes rechts (Zelda levens)
        for i in range(3):
            hx = 88 + i * 13; hy = 8
            d.pixel(hx + 1, hy, 1);    d.pixel(hx + 3, hy, 1)
            d.hline(hx,     hy + 1, 5, 1)
            d.hline(hx,     hy + 2, 5, 1)
            d.hline(hx + 1, hy + 3, 3, 1)
            d.pixel(hx + 2, hy + 4, 1)

        # Fonkelende sterretjes links
        for i, (sx, sy) in enumerate(((4, 6), (14, 18), (6, 30), (22, 10), (18, 36))):
            if (frame // 4 + i) % 3 != 0:
                d.pixel(sx, sy, 1)
                d.pixel(sx + 1, sy, 1)
                d.pixel(sx, sy + 1, 1)
                d.pixel(sx + 1, sy + 1, 1)

        d.show()

    def _draw_sonic_animation(self, frame, intensity):
        """Green Hill Zone: rolling hills, detailed Sonic sprite, rings, speed lines."""
        d = self.display
        d.fill(0)

        # Sky: distant checkered pattern (GHZ style)
        for sy in range(0, 20, 4):
            for sx in range(0, 128, 8):
                if (sx // 8 + sy // 4) % 2 == 0:
                    d.fill_rect(sx, sy, 4, 2, 1)

        # Far rolling hill (slow)
        ho1 = (frame // 4) % 64
        for hx in range(0, 128):
            hpeak = 20 - 8 * abs(((hx + ho1) % 64) - 32) // 32
            d.vline(hx, hpeak, 22 - hpeak, 1)

        # Near hill (faster, higher)
        ho2 = (frame // 2) % 48
        for hx in range(0, 128):
            hpeak = 26 - 6 * abs(((hx + ho2) % 48) - 24) // 24
            d.vline(hx, hpeak, 30 - hpeak, 1)

        # Ground
        d.fill_rect(0, 30, 128, 6, 0)
        d.hline(0, 30, 128, 1)
        d.hline(0, 36, 128, 1)
        # Checkerboard tiles scrolling
        tile_off = (frame * 3) % 16
        for tx in range(0, 128, 16):
            x = tx - tile_off
            d.fill_rect(x, 31, 8, 5, 1)
        d.fill_rect(0, 37, 128, 27, 1)

        # Speed lines behind Sonic
        sx0 = 28
        for i, (ly, llen) in enumerate(((33, 14), (35, 18), (37, 12))):
            d.hline(sx0 - llen - i * 3, ly, llen, 0)

        # Sonic sprite (12x14) at fixed position
        sx, sy = 30, 17
        leg = (frame // 2) % 4
        # Spines (3 spikes going back-left)
        d.line(sx + 4, sy, sx, sy - 3, 1)
        d.line(sx + 6, sy + 1, sx + 2, sy - 2, 1)
        d.line(sx + 8, sy + 2, sx + 5, sy - 1, 1)
        # Head
        d.fill_rect(sx + 4, sy, 8, 7, 1)
        d.pixel(sx + 10, sy + 2, 0)  # eye
        # Torso
        d.fill_rect(sx + 3, sy + 7, 7, 5, 1)
        # Arm
        if frame % 4 < 2:
            d.fill_rect(sx + 10, sy + 8, 4, 2, 1)
        else:
            d.fill_rect(sx + 10, sy + 9, 4, 2, 1)
        # Legs
        if leg < 2:
            d.fill_rect(sx + 3, sy + 12, 3, 4, 1)
            d.fill_rect(sx + 7, sy + 10, 3, 4, 1)
        else:
            d.fill_rect(sx + 3, sy + 10, 3, 4, 1)
            d.fill_rect(sx + 7, sy + 12, 3, 4, 1)
        # Red shoe hint
        d.hline(sx + 2, sy + 14, 5, 1)
        d.hline(sx + 6, sy + 13, 5, 1)

        # Ring (right side, bobbing)
        ry = 20 + ((frame // 5) % 3)
        d.rect(90, ry, 10, 10, 1)
        d.rect(92, ry + 2, 6, 6, 0)
        # Shine on ring
        if (frame // 4) % 2 == 0:
            d.pixel(91, ry + 1, 1)
            d.pixel(92, ry, 1)

        # HUD
        d.text("SONIC", 68, 0, 1)
        score = (frame * 77) % 9999
        d.text(str(score), 68, 10, 1)
        if (frame // 8) % 2 == 0:
            d.fill_rect(0, 56, 128, 8, 1)
            d.text("ALARM!", 40, 56, 0)
        else:
            d.text("ALARM!", 40, 56, 1)
        d.show()

    def _draw_metroid_animation(self, frame, intensity):
        """Samus in Chozo ruins: detailed armor silhouette, charging beam, lava glow."""
        d = self.display
        d.fill(0)

        # Lava at bottom (pulsing)
        lava_y = 52 + (frame // 6) % 3
        d.fill_rect(0, lava_y, 128, 64 - lava_y, 1)
        for bx in range(0, 128, 12):
            boff = (bx + frame * 2) % 24
            by = lava_y - 2 - (boff % 5)
            d.fill_rect(bx, by, 6, lava_y - by, 0)

        # Pillars (Chozo ruins)
        for px in (2, 108):
            d.fill_rect(px, 20, 14, lava_y - 20, 1)
            d.fill_rect(px - 2, 18, 18, 4, 1)  # capital
            d.fill_rect(px - 2, lava_y - 4, 18, 4, 1)  # base
            for gy in range(24, lava_y - 4, 8):
                d.hline(px + 1, gy, 12, 0)

        # Samus armor silhouette (centered)
        sx, sy = 52, 4
        # Helmet (round top)
        d.fill_rect(sx + 4, sy, 16, 4, 1)
        d.fill_rect(sx + 2, sy + 2, 20, 10, 1)
        d.fill_rect(sx + 6, sy + 5, 12, 5, 0)  # visor cutout
        d.fill_rect(sx + 8, sy + 6, 8, 3, 1)   # visor glow
        # Shoulders
        d.fill_rect(sx, sy + 10, 8, 8, 1)
        d.fill_rect(sx + 16, sy + 10, 8, 8, 1)
        d.fill_rect(sx, sy + 10, 8, 3, 1)  # shoulder cap
        d.fill_rect(sx + 16, sy + 10, 8, 3, 1)
        # Torso
        d.fill_rect(sx + 6, sy + 12, 12, 10, 1)
        d.hline(sx + 8, sy + 16, 8, 0)  # chest detail
        # Arm cannon (right)
        cannon_len = 12 + ((frame // 3) % 4)
        d.fill_rect(sx + 24, sy + 13, cannon_len, 5, 1)
        d.fill_rect(sx + 22, sy + 12, 4, 7, 1)  # cannon joint
        # Charge ball at cannon tip
        pulse = (frame // 2) % 6
        tip_x = sx + 24 + cannon_len
        if pulse < 3:
            d.fill_rect(tip_x, sy + 13, 4, 5, 1)
        else:
            d.fill_rect(tip_x - 1, sy + 12, 6, 7, 1)
            if pulse == 5:
                d.pixel(tip_x + 2, sy + 15, 0)  # core
        # Left arm
        d.fill_rect(sx - 4, sy + 13, 12, 4, 1)
        # Legs
        d.fill_rect(sx + 5, sy + 22, 5, 10, 1)
        d.fill_rect(sx + 14, sy + 22, 5, 10, 1)
        d.fill_rect(sx + 3, sy + 30, 7, 4, 1)  # boot left
        d.fill_rect(sx + 14, sy + 30, 7, 4, 1)  # boot right

        # Energy bar (top)
        charge = max(0, min(100, int(intensity)))
        d.text("E", 0, 0, 1)
        d.rect(10, 1, 52, 6, 1)
        d.fill_rect(11, 2, charge * 50 // 100, 4, 1)

        if (frame // 8) % 2 == 0:
            d.fill_rect(0, 56, 128, 8, 1)
            d.text("ALARM!", 40, 56, 0)
        else:
            d.text("ALARM!", 40, 56, 1)
        d.show()

    def _draw_pokemon_animation(self, frame, intensity):
        """Gen-1 battle scene: proper HUD boxes, Pikachu silhouette, trainer, pokeball."""
        d = self.display
        d.fill(0)

        # Battle field divider
        d.hline(0, 28, 128, 1)
        d.hline(0, 29, 128, 1)

        # Pikachu-like silhouette (enemy, top-right)
        px, py = 76, 2
        # Ears (pointy)
        d.line(px + 4, py, px + 2, py - 4, 1)
        d.line(px + 2, py - 4, px + 1, py - 4, 1)
        d.line(px + 9, py, px + 11, py - 4, 1)
        d.line(px + 11, py - 4, px + 12, py - 4, 1)
        # Head
        d.fill_rect(px + 1, py, 12, 10, 1)
        d.pixel(px + 3, py + 3, 0)  # left eye
        d.pixel(px + 9, py + 3, 0)  # right eye
        d.pixel(px + 5, py + 6, 0)  # nose
        d.pixel(px + 7, py + 6, 0)
        # Cheeks (round)
        d.fill_rect(px - 1, py + 4, 3, 3, 1)
        d.fill_rect(px + 12, py + 4, 3, 3, 1)
        # Body
        d.fill_rect(px + 2, py + 10, 10, 7, 1)
        # Tail (lightning bolt hint)
        d.line(px + 12, py + 12, px + 16, py + 8, 1)
        d.line(px + 16, py + 8, px + 20, py + 14, 1)
        # Legs
        d.fill_rect(px + 3, py + 17, 3, 4, 1)
        d.fill_rect(px + 8, py + 17, 3, 4, 1)

        # Trainer silhouette (player, bottom-left)
        tx, ty = 8, 16
        d.fill_rect(tx + 3, ty, 6, 5, 1)   # head
        d.fill_rect(tx + 2, ty + 5, 8, 8, 1)  # body
        d.fill_rect(tx, ty + 6, 3, 5, 1)   # arm (throwing)
        d.fill_rect(tx + 9, ty + 7, 3, 4, 1)
        d.fill_rect(tx + 3, ty + 13, 3, 5, 1)  # legs
        d.fill_rect(tx + 6, ty + 13, 3, 5, 1)

        # Pokeball arc
        progress = (frame * 2) % 80
        bx = 22 + progress
        arc_h = 22 - ((progress - 40) * (progress - 40)) // 73
        by2 = max(6, arc_h)
        d.rect(bx, by2, 6, 6, 1)
        d.hline(bx, by2 + 3, 6, 1)  # equator line
        d.pixel(bx + 2, by2 + 2, 0)
        d.pixel(bx + 3, by2 + 2, 0)  # button

        # Enemy HP box (top-left)
        d.rect(0, 0, 62, 12, 1)
        d.text("PIKACHU", 2, 1, 1)
        d.rect(0, 9, 62, 4, 1)
        hp = max(0, min(100, int(intensity)))
        d.fill_rect(1, 10, hp * 60 // 100, 2, 1)

        # Player status box bottom
        d.rect(66, 30, 62, 12, 1)
        d.text("TRAINER", 68, 31, 1)
        d.rect(66, 39, 62, 4, 1)
        d.fill_rect(67, 40, 60, 2, 1)

        # Battle text box
        d.rect(0, 45, 128, 19, 1)
        blink = (frame // 6) % 2
        if blink == 0:
            d.text("WAKE  UP!", 4, 48, 1)
        else:
            d.text("WAKE  UP!", 4, 56, 1)
        d.pixel(120, 56, 1)
        d.pixel(122, 54, 1)
        d.pixel(124, 56, 1)
        d.show()

    def _draw_tetris_animation(self, frame, intensity):
        """Tetris: detailed board with grid, filled stack, active piece, next+score panel."""
        d = self.display
        d.fill(0)

        bx, by, cell = 4, 2, 5
        cols, rows = 9, 12

        # Board outline + grid
        d.rect(bx - 1, by - 1, cols * cell + 2, rows * cell + 2, 1)
        for gx in range(1, cols):
            d.vline(bx + gx * cell, by, rows * cell, 1)
        for gy in range(1, rows):
            d.hline(bx, by + gy * cell, cols * cell, 1)

        # Static stack (deterministic per frame-epoch)
        epoch = frame // 60
        stack_heights = [(4 + ((i * 5 + epoch * 3) % 5)) for i in range(cols)]
        for col in range(cols):
            sh = stack_heights[col]
            for row in range(sh):
                ry = rows - 1 - row
                cx2 = bx + col * cell + 1
                cy2 = by + ry * cell + 1
                d.fill_rect(cx2, cy2, cell - 2, cell - 2, 1)
                # Checker pattern on filled cells
                if (col + row) % 2 == 0:
                    d.pixel(cx2 + 1, cy2 + 1, 0)

        # Line clear flash
        full_row = rows - 1
        all_full = all(stack_heights[c] >= 1 for c in range(cols))
        if all_full and (frame // 3) % 2 == 0:
            d.fill_rect(bx, by + full_row * cell, cols * cell, cell, 0)

        # Falling piece
        shape = (frame // 24) % 5
        max_drop = (rows - max(stack_heights)) * cell
        drop = (frame * 2) % max(cell, max_drop)
        px2 = bx + (1 + (frame // 40) % (cols - 3)) * cell
        py2 = by + drop
        if shape == 0:   # I (horizontal)
            for i in range(4):
                d.rect(px2 + i * cell, py2, cell - 1, cell - 1, 1)
        elif shape == 1: # O
            d.rect(px2, py2, cell - 1, cell - 1, 1)
            d.rect(px2 + cell, py2, cell - 1, cell - 1, 1)
            d.rect(px2, py2 + cell, cell - 1, cell - 1, 1)
            d.rect(px2 + cell, py2 + cell, cell - 1, cell - 1, 1)
        elif shape == 2: # T
            for i in range(3):
                d.rect(px2 + i * cell, py2, cell - 1, cell - 1, 1)
            d.rect(px2 + cell, py2 + cell, cell - 1, cell - 1, 1)
        elif shape == 3: # S
            d.rect(px2 + cell, py2, cell - 1, cell - 1, 1)
            d.rect(px2 + 2 * cell, py2, cell - 1, cell - 1, 1)
            d.rect(px2, py2 + cell, cell - 1, cell - 1, 1)
            d.rect(px2 + cell, py2 + cell, cell - 1, cell - 1, 1)
        else:            # L
            for i in range(3):
                d.rect(px2, py2 + i * cell, cell - 1, cell - 1, 1)
            d.rect(px2 + cell, py2 + 2 * cell, cell - 1, cell - 1, 1)
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
